ShugoYabuno/project-hanoji/marketing/sns/posts/index.md

# SNS投稿状況インデックス

最終更新: 2026-03-29

---

## 投稿済み（確認・記入用）

| 日付 | プラットフォーム | テーマ | URL / メモ | エンゲージメント |
|---|---|---|---|---|
| - | X | | | |
| - | note | | | |

※ Claude Desktopでアナリティクスを確認後、ここに記入してください。

---

## ブログ記事（note）の公開状況

| タイトル | 状態 | 公開URL |
|---|---|---|
| 自作レバーレス製作記 Vol.1：理想の角度を求めて失敗した話（v1） | 下書き済み | 未公開 |
| 自作レバーレス製作記 Vol.2：一体成形で「全部入り」を試みたら、印刷が地獄だった話（v2） | 下書き済み | 未公開 |
| v3〜v5 記事 | 未着手 | - |

---

## 下書き済みツイート

| ファイル | テーマ | 状態 |
|---|---|---|
| [2026-03-29_v5進捗.md](2026-03-29_v5進捗.md) | v5試作の進捗報告 | 下書き |
| [2026-03-29_コンセプト紹介.md](2026-03-29_コンセプト紹介.md) | なぜ作っているかの原点 | 下書き |
| [2026-03-29_v1失敗の話.md](2026-03-29_v1失敗の話.md) | v1の失敗→note誘導 | 下書き |
