ShugoYabuno/project-hanoji/content/blog/ideas/ideas.md

# ブログ記事・コンテンツアイデア帳

## 執筆方針
- **透明性 (Build in Public)**: 開発の過程、失敗、悩みもすべて公開し、ストーリーに共感してもらう。
- **専門性**: エルゴノミクスの知識や、なぜその形状に至ったかのロジックを語る。

---

## 記事ネタリスト

### 1. 宣言・コンセプト (The "Why")
**タイトル案**: 平面レバーレスで手首を痛めた私が、理想の「八の字」コントローラーを作るまで
- **構成**:
    - 既存レバーレスへの不満（手首の痛み、窮屈さ）
    - 「回内」と「回外」の解剖学的説明（図解を入れると良い）
    - Project Hanoji の構想（ラフスケッチ公開）
    - 目標：長くゲームを楽しむためのデバイスを作る

### 2. 開発ログ (The "How")
**タイトル案**: Project Hanoji 開発日誌 #1：3Dプリンターとの格闘
- **構成**:
    - 現在のFusion 360モデルの紹介
    - 印刷失敗写真（スパゲッティ状態など）をあえて載せる
    - 試作1号機の握り心地レビュー
    - 次の課題

### 3. こだわりポイント解説
**タイトル案**: なぜその角度？ボタン配置の数ミリ単位のこだわり
- **構成**:
    - 指の長さの違いに合わせたボタン配置
    - 天板の傾斜角（テント角）の検証プロセス
    - 15度？ 20度？ どの角度が最も楽か実験してみた

### 4. 部品選びの旅
**タイトル案**: 最高の打鍵感を求めて。キースイッチ選定会議
- **構成**:
    - 銀軸、ロープロファイルなど、採用候補のスイッチ比較
    - 静音性 vs クリック感
    - 実際に採用するスイッチの決定理由

### 5. マーケティング・戦略（裏側公開）
**タイトル案**: 個人開発デバイスをどうやって届けるか？Hanojiの販売戦略
- **構成**:
    - 個人メーカーとしての悩み
    - 価格設定の裏話
    - パッケージングへのこだわり

---

## SNS (X/Instagram) 投稿ネタ
- **[画像]**: 3D CADのワイヤーフレーム画像「設計中...」
- **[動画]**: 3Dプリンターが動いているタイムラプス
- **[画像]**: 試作機の基板配線の様子「配線地獄なう」
- **[質問]**: 「カラーバリエーション、どっちが好きですか？（A: マットブラック / B: ホワイト）」アンケート機能活用
