ShugoYabuno/project-hanoji/content/assets/prototypes/1/feedback.md

# プロトタイプ1 (v1) フィードバック

作成日: 2026-01-15
対象: 試作機v1 (@content/assets/prototypes/1)

## 検証結果・感想

### 1. 保持と安定性の問題
- **現象**: 傾斜（テンティング）がついているが、パームレストがついていない。
- **問題点**: 手が滑りやすく、常に手を特定の位置に保持するために力が必要となる。
- **対策案**:
    - 傾斜に追従するパームレストの実装が必須。
    - 表面の滑り止め加工や素材の検討が必要。

### 2. 角度設定の問題（手首への負荷）
- **現象**: テンティング角（z軸回転）はついているが、xy平面の角度（ハの字の開き角）がついていない。
- **問題点**:
    - 腕の自然な進入角度に対してキー配置が適合していない。
    - 結果として、手首を甲側（背屈方向）に無理に曲げる動作が強要される。
    - 手首への負荷が大きく、エルゴノミクスの目的（負荷軽減）が達成できていない。
- **対策案**:
    - テンティングだけでなく、左右のユニットをハの字に開く（またはその角度をつける）設計が必要。
