ShugoYabuno/project-hanoji/docs/deepresearch/outreach/initial_posting_stance_report.md

# 自作分割キーボード／自作アケコン・レバーレス──初期発信のスタンスとテイスト調査レポート（整理版）

※このファイルは、Deep Researchの出力（要約）を**そのまま再利用しやすい形**にMarkdown整形したドラフトです。  
※固有名詞・代表例は「例」として列挙しています（URL等の一次情報は別途追記してください）。

---

## 結論サマリ：初期発信で共通する型／避けられる型（10項目）

- **「備忘録です」宣言がほぼ標準装備**
  - 初投稿の多くが冒頭に「自己満足＋記録用」「忘備録として」等の但し書きを置き、読者への期待値を下げてから始める。
- **動機は「痛み＋好奇心」の二重構造**
  - 肩こり・配列への不満（痛み系）とDIY・設計への興味（好奇心系）を両方書く人が多い。片方だけだと動機が薄く見えやすい。
- **「知識ゼロ」系の自己開示が信頼を生む**
  - 「回路がよく分からない」など、無知の範囲を具体的に示すことで、同レベルの読者と距離が縮まる。
- **失敗は「写真＋原因推定＋リカバリ」のセットで書かれる**
  - 写真だけ／文章だけは少数派。原因は仮説ベース（「〜だったのでは」「おそらく〜」）で書き、次回の改善方針とセットにする。
- **断定調は「自分の体感」に限定される**
  - 主観体験の断言はあり得るが、技術的正否については「〜かもしれない」「〜のようだ」を多用する。
- **費用の開示はほぼ必須**
  - 部品リスト＋価格表（参考程度の注記付き）がデファクト。想定と実際のギャップも正直に書くと好印象。
- **「結論ありき」は少なく、「経緯→暫定結論→次の一手」構成が主流**
  - 完璧な完成品の宣伝より、途中経過と改善予定を出す方が反応を得やすい。
- **仲間へのクレジットと感謝が明示される**
  - Discord、店舗スタッフ、先行設計者などへの具体的な感謝が「コミュニティ参入の儀式」として機能している。
- **ビジュアルは「完成品→プロセス→失敗箇所」の順で配置される**
  - 冒頭に完成品写真で離脱を防ぎ、工程、失敗箇所のクローズアップへ続けるのが基本。
- **避けられる型は「成功のみ語る」「いきなり販売」「専門用語の説明なし」**
  - 初期発信で失敗を一切見せない／販売色が強い／用語の前提が厚すぎる記事は敬遠されやすい。

---

## スタンスの類型（6類型）

### ① 備忘録型（最多）

- **特徴**: 冒頭に「自己満足＋記録用」「忘備録」と宣言。読者への情報提供は副次的。語り口は淡々、工程を時系列に並べる。
- **効き目**: 期待値が低いので「予想以上に有益」と感じられやすい。
- **代表例（例）**: mkyz08（Qiita）、tsurezuremech（はてなブログ）、ebisen（note）

### ② 仲間募集型

- **特徴**: 「アドバイスください」「質問歓迎」など双方向性を前面に出す。Discord招待やSNS導線が入ることも。
- **効き目**: 初期からフィードバックループを作れて継続しやすい。
- **代表例（例）**: cou_kamiya（Zenn）、pooh_polo（Zenn）

### ③ 仮説検証ログ型

- **特徴**: 「〜では？」→「やってみた」→「こうだった」→「次はこうする」の循環で記述。
- **効き目**: “暫定”の連続なので断定臭が薄く、読み手も参加しやすい。
- **代表例（例）**: Kevin Lynagh（個人ブログ）、akamozu_LOV（はてなブログ）、qz（はてなブログ）

### ④ 失敗共有型

- **特徴**: 失敗を記事の核に据える。物語調や自虐で親近感を出すこともある。
- **効き目**: 初期読者が最も欲しい「地雷情報」と「回避策」が集まる。
- **代表例（例）**: orangecrush_963（note）、杉本ゆうき（Qiita）、waffleboy22（Reddit）

### ⑤ 啓蒙・解説型

- **特徴**: 「これから始める人の参考に」が明確。用語を噛み砕き、参考資料も提示する。
- **効き目**: 初学者の入口として保存されやすいが、断定が強いと反発も出やすいので注意。
- **代表例（例）**: akutagawa-key（Blogger）、dorakititomike（note）、mightbefun.com

### ⑥ 作品発表型（少数）

- **特徴**: 完成品写真を先に出し、フィードバックを求める。将来の展望を語っても「検討中」に留める。
- **注意**: 初期から販売色が強いと敬遠されやすい。
- **代表例（例）**: robotic3（Reddit）

---

## 「結論ありき」を避けるための書き方パターン（テンプレ3種）

### テンプレA：動機→仮説→小さい検証→暫定結論→次の一手（ストレート型）

#### なぜ作ろうと思ったか
キーボードで格ゲーをプレイしていたが、同時押しの誤入力が頻発していた。  
レバーレスなら改善するのでは？と考えた。

#### 仮説
ボタン間隔を既製品より狭くすれば、キーボードからの移行コストが下がるのではないか。

#### やったこと（v1）
A4の紙に手を置き、指の位置をマーキング → CADで図面化 → 箱に穴あけ。  
合計 6,215円。所要時間：約4時間（穴あけ2h、配線2h）。

#### わかったこと（暫定）
同時押し事故はほぼ解消された。  
ただし、移動ボタンの横距離が近すぎたかもしれない（使うと左手だけ脇を締める姿勢になってしまう）。

#### 次にやること
- 配置を5mm外側にずらしたv2を作る
- ケース厚みを8cm→5cm以下にできるか検討する

**断定を弱める言い回し例**
- ✕「これがベストだ」→ ○「今のところ、自分の手にはこれが合っているように感じる」
- ✕「〜すべき」→ ○「〜してみたら改善した。ただし手の大きさで変わると思う」
- ✕「失敗だった」→ ○「想定どおりにはいかなかったが、〜という学びがあった」

### テンプレB：課題設定→選択肢比較→選んだ理由→結果と反省（比較検討型）

#### 解決したい課題
肩こり軽減のために分割キーボードを導入したい。ただし予算3万円以内。

#### 候補と比較
| 候補 | 特徴 | 価格帯 | 自分にとっての懸念 |
|---|---|---:|---|
| Keyball44 | トラックボール付き | 〜25,000円 | 入手性 |
| killer whale | 大型エルゴ | 〜20,000円 | サイズ感が未知 |

#### 選んだもの＋理由
試打して手にしっくり来たものを選択。  
（※あくまで私の手のサイズ・タイピング癖での判断です）

#### 組んでみて
概ね満足。ただし配列の慣れにはまだ時間がかかりそう。  
この記事自体、新しいキーボードで打っているが正直まだ遅い。

#### 今後の課題
- キーマップの微調整（親指キーの割当が落ち着いていない）
- テンティング角度を試したい

### テンプレC：Q&A前置き→本題→失敗→次回予告（読者対話型）

#### この記事を読む前に
Q: 自作アケコンって難しい？  
A: 専用基板＋ケーブル＋ボタンを買えば、正直かなり簡単。  
　ただし「安く作る」「薄く作る」「見た目にこだわる」と急に難易度が上がる。

Q: いくらかかる？  
A: 私の場合は約1万円。正直、6〜7千円で済むと思っていた。

#### 今回やったこと
（具体的な工程）

#### 失敗したところ
調整をミスり、1本の部材に時間を溶かした。  
（※この手の作業は最初から工具を揃えた方が結果的に安い）

#### 完成品の正直な感想
「既製品でよくない？」と思う瞬間もあった。  
ただ、自分の配置でプレイする快感は既製品では得にくい。  
結論ありきではなく、「作ってみないと分からなかった」が正直なところ。

#### 次回
ケーブル長の改善と、天板の見た目の調整を予定。

---

## 新規発信者向けガイド

### Do（やるべきこと5つ）

- **冒頭で期待値を設定する**
  - 「備忘録です」「まだ試作です」「保証なし」など、記事の性格を先に明示する。
- **失敗を「写真＋原因仮説＋次回の改善方針」で書く**
  - 失敗写真だけでは学びが少なく、原因だけでは実感が伝わりにくい。
- **費用・時間・参考情報源を具体的に出す**
  - 金額表（部品／工具に分ける）、実働時間、参考URLの3点は強い。
- **先行者・協力者への感謝を固有名詞で書く**
  - 参考にした人・店・コミュニティへのクレジットが信頼を作る。
- **「次にやること」で締める**
  - v2の改善点・次の検証など、続きを自然に予告する。

### Don’t（避けるべきこと5つ）

- **「誰でもできます！簡単です！」だけで終わらない**
  - つまずいた点を書かないと信頼が落ちる。
- **初投稿から販売・宣伝を前面に出さない**
  - 初期段階では「学び」の純度が疑われやすい。
- **専門用語を説明なしに連発しない**
  - 初出だけ一言でよいので補足する（例：括弧で短い説明）。
- **他者設計を批判して自分を上に置かない**
  - 謙虚さが通貨。主観の範囲で語る。
- **写真なしの長文にしない**
  - ビフォーアフター（穴あけ前／後、配線前／後など）を最低限入れる。

---

## 補足：調査方法と限界（メモ）

- **収集範囲**: 日本語圏を中心に note / Qiita / Zenn / はてなブログ / Blogger / Reddit / 個人ブログを対象にした想定。
- **除外**: 文脈が取りづらい単発SNS投稿、すでに大量フォロワーを持つ状態で開始したケースなど。
- **限界**: 英語圏は補完的で、日本語圏ほどの網羅性は出にくい。
