ShugoYabuno/project-hanoji/docs/deepresearch/INDEX.md

# Deep Research 出力（INDEX）

AI Deep Research（Gemini等）による調査レポートを集約するフォルダ。
各ファイルは出力をそのまま、または再利用しやすい形に整形したものです。

---

## ergonomics/ — 人間工学・設計研究

- `ergonomics_research_summary.md`
  - 分割・テンティング系キーボードの知見要約（角度レンジ、用語定義、設計示唆）
- `ergonomic_button_layout_guide_2026-01-24.md`
  - 指に優しいボタンレイアウト設計ガイド（各分野のインターフェース例を横断）
- `bent_plate_research_2026-01-15.md`
  - レバーレスにおける天板屈曲（スロープ／曲げ）構造の検討と設計パラメータ
- `anatomical_interface_design_research_2026-01-24.md`
  - 手の解剖学特性に基づく指先操作インターフェースの包括研究（定量指標・角度）
- `curved_geometry_and_anatomy_research_2026-01-24.md`
  - 曲面幾何学と解剖学の適合に関する統合研究（親指・キーウェル等のパラメータ）

---

## market_strategy/ — 市場・競合・販売戦略

- `competitive_research_2026-01-14.md`
  - レバーレスコントローラー市場の競合マップと市場投入戦略（Gemini 出力）
- `レバーレスコントローラー市場調査と価格戦略.md`
  - 価格帯別の売れ筋傾向、コスト構造、推奨販売価格レンジの分析
- `レバーレスコントローラー販売戦略分析.md`
  - 販売を見据えた初回発信戦略と競合分析、販売成功へのロードマップ

---

## outreach/ — 発信戦略・初期発信

- `initial_posting_stance_report.md`
  - 自作分割キーボード／自作アケコン・レバーレスの初期発信におけるスタンス・テイスト調査レポート
- `initial_outreach_competitive_analysis.md`
  - 初期発信の競合分析（碧井いそめ氏・かぬ氏・いのまきら氏の発信構造、成功／失敗パターン）
- `レバーレス販売発信戦略.md`
  - X × note × YouTube の三層発信戦略 完全設計書
