ShugoYabuno/project-hanoji/docs/deepresearch/outreach/レバーレス販売発信戦略.md

# 自作レバーレスコントローラー販売のための発信戦略 完全設計書

---

## 結論：最適な投稿方針（1案）

**X（ほぼ毎日）× note（週1本）× YouTube（月2本）** の三層構造で、初期3か月は「販売」の文字を出さず、**「作る人」としてのキャラクター確立** に全リソースを投下する。

**運用比率：X 50% ／ note 30% ／ YouTube 20%**

- **X** ＝ フロー型。制作の「今」を高頻度で見せる場。写真1枚＋短文で日常的な接触頻度を確保する[^17]
- **note** ＝ ストック型。設計思想・試作記録・技術解説を体系的に蓄積し、検索経由での新規流入を狙う[^24]
- **YouTube** ＝ 体験証明型。組み立て配信・打鍵音・実際のプレイ映像で「この製品は本物だ」と伝える[^42]

---

## 1. 調査から判明した成功パターン3つ

### ① 制作過程の「全公開」戦略

碧井工房（JumpHack）は、Xで制作過程を日々ポストし、BOOTHと自社ストアで組み立てキット＋完成品の2形態で販売している[^33][^39]。YouTubeでは組み立てライブ配信を行い、視聴者がリアルタイムで質問できる形式を採用した[^42]。「プロトタイプ段階から公開する」「図面データすら公開する」という透明性が、ニッチコミュニティでの信頼獲得に直結している。

### ② 媒体横断のクロスポスト設計

投稿データ分析では、noteとXを連携させることで単独利用時よりリーチが伸びる傾向が示唆されている[^17]。具体的には、noteの冒頭部分だけXで紹介し「続きはnoteで」と誘導するパターン、Xで集まった質問をnoteでまとめ記事化するパターンが特に有効である。

### ③ 「ユーザー参加型」のコミュニティ形成

P-3 Controller（ぴくるす）はXでプレゼント企画を実施し、レバーレス完成品を提供することでフォロワーとの接点を生んでいる[^23][^26]。また遊舎工房（自作キーボード）は「コミュニティと一緒に成長する」を運営方針に掲げ、グループバイで300台（国内50台・海外250台）を販売した実績がある[^20]。

---

## 2. 避けるべきパターン3つ

### ❌ 初期から「販売臭」を出す
noteに投稿する記事が最初から商品の宣伝ばかりでは、読者はなかなか増えない。まず消費者目線で役に立つ情報を発信し、フォロワーを増やしながらブランドへの共感を育てることが先決[^27]。

### ❌ 過剰投稿によるファン離れ
投稿頻度が高すぎるとアンフォロー率が上がる傾向がある。質と量のバランスが崩れると逆効果になりやすい[^17]。

### ❌ 同一コンテンツのコピー投稿
noteの記事をそのままXのスレッドに貼り付ける、リンクだけを機械的に共有する自動投稿は効果が限定的。各プラットフォームで異なる価値を提供する必要がある[^17]。

---

## 3. テーマ配分の最適比率

| テーマカテゴリ | 全体比率 | 主な媒体 | 具体例 |
|---|---|---|---|
| 試作記録・制作過程 | 30% | X, YouTube | 部材到着、組み立て中の写真、ライブ配信 |
| 技術解説・設計思想 | 25% | note | GP2040-CE解説、ボタンレイアウト理論、素材選定理由 |
| 失敗談・改善プロセス | 15% | note, X | 基盤ネジ穴の失敗[^16]、設計ミスからの修正 |
| 使用感・プレイ体験 | 15% | YouTube, X | 打鍵音ASMR、実プレイ映像、操作比較 |
| コミュニティ交流 | 10% | X | 他制作者の紹介、質問回答、アンケート |
| 販売準備・告知 | 5% | X, note | 価格検討中の匂わせ、予約開始告知 |

**重要：初期3か月は「販売準備・告知」の比率を5%以下に抑え、試作記録＋技術解説で全体の55%を占めるようにする。**

---

## 4. 媒体別の役割と最適投稿サイクル

### X（フロー＝日常接触）

- **頻度**：ほぼ毎日（最低でも数日に1回は継続する）[^17]
- **最適時間帯**：平日昼・夕方に反応が伸びやすい傾向[^17]
- **コンテンツ形式**：写真1枚＋短文、スレッド形式の制作メモ、アンケート
- **週1-2回**はスレッド形式での深掘りコンテンツを投稿

### note（ストック＝資産蓄積）

- **頻度**：週1本（個人アカウントは週1-2回の継続が現実的）[^17][^22]
- **最適時間帯**：日曜夜・平日夜に反応が伸びやすい傾向[^17]
- **コンテンツ形式**：2,000-5,000字程度の長文が目安。月1回は深掘り記事を入れる[^17]
- **SEO意識**：「レバーレス 自作」「アケコン 作り方」等のキーワードをタイトル・見出しに配置[^24]

### YouTube（体験証明＝信頼構築）

- **頻度**：月2本（負担とクオリティのバランス）
- **コンテンツ形式**：制作工程動画（長尺OK。作りたい人向けは長めの方が評価されやすい傾向）[^31]、組み立てライブ配信、打鍵音・使用感レビュー
- **概要欄にnoteとXへのリンクを必ず設置**[^24]

---

## 5. 最初の3か月の投稿設計テンプレート

### 第1フェーズ（1か月目）：「何を作ろうとしているか」を見せる

**目標**：格ゲーコミュニティ内での認知獲得、フォロワー50人

| 週 | X（毎日） | note（週1） | YouTube |
|---|---|---|---|
| 1週目 | 使用素材の写真、RP2040-Picoの紹介 | 「なぜ自作レバーレスを作るのか」（設計思想・動機） | — |
| 2週目 | ボタンレイアウトの検討過程、CAD画面 | 「レバーレスの仕組みをゼロから解説」（技術入門） | 部材開封・紹介動画（5-8分） |
| 3週目 | 発注したアクリル板の到着報告、寸法確認 | 「試作1号機の設計で考えたこと」（素材・構造選定） | — |
| 4週目 | 組み立て開始の写真、困った点メモ | 「試作1号機の組み立てで起きたトラブル」（失敗談） | 組み立て過程のタイムラプス動画 |

### 第2フェーズ（2か月目）：「試行錯誤の過程」を共有する

**目標**：フォロワー150人、note記事のスキ数平均20以上

| 週 | X（毎日） | note（週1） | YouTube |
|---|---|---|---|
| 5週目 | 試作1号機の完成写真、打鍵テスト | 「1号機完成レビュー：良い点と改善点」 | 打鍵音ASMR＋実プレイ映像 |
| 6週目 | 改善ポイントの洗い出し、他製品との比較 | 「GP2040-CEのファームウェア設定ガイド」（技術解説） | — |
| 7週目 | 2号機の設計変更点、スケッチ公開 | 「ボタン配置の人間工学を考える」（設計思想） | — |
| 8週目 | 2号機組み立て中、「これ売ってほしい？」アンケート | 「1号機→2号機で何を変えたか」（改善記録） | 2号機の組み立てライブ配信 |

### 第3フェーズ（3か月目）：「完成度の高さ」を証明し、販売を匂わせる

**目標**：フォロワー300人、DM/リプで「販売しないの？」の声が出る

| 週 | X（毎日） | note（週1） | YouTube |
|---|---|---|---|
| 9週目 | 2号機完成写真（高品質な撮影）、仕様スペック | 「2号機完全レビュー：市販品との比較」 | 完成品レビュー＋プレイ映像（勝率変化等） |
| 10週目 | オフ対戦会での使用報告、他プレイヤーの反応 | 「自作レバーレスにかかったコスト全公開」（費用明細） | — |
| 11週目 | 「量産に向けて検討中」と自然に言及 | 「3か月の制作で学んだこと総まとめ」 | 1号機→2号機の進化を振り返る比較動画 |
| 12週目 | 販売形態の検討（キット or 完成品）アンケート | 「販売に向けて：価格設定の考え方」 | — |

---

## 6. 初期フェーズで「販売臭」を出す最適濃度

**結論：最初の8週間は販売意図ゼロ。9週目以降に10-15%程度まで徐々に引き上げる。**

| フェーズ | 期間 | 販売臭の濃度 | 具体的な匂わせ方 |
|---|---|---|---|
| 純粋な制作者 | 1-4週 | 0% | 一切販売に言及しない。「自分が使いたくて作っている」スタンス |
| 共感者の登場 | 5-8週 | 5% | 「欲しいって言ってくれる人がいて嬉しい」とリプ引用RT程度 |
| 需要の可視化 | 9-10週 | 10% | Xアンケート「もし売るとしたらいくらなら買う？」 |
| 販売の自然な流れ | 11-12週 | 15% | 「量産コスト計算中」「販売方法を調べている」と過程を公開 |
| 販売開始 | 13週以降 | 20% | BOOTH/BASEリンク公開。ただし投稿全体の8割は制作・技術コンテンツ維持 |

碧井工房（JumpHack）のケースでは、プロトタイプ段階から「実験的な開発機なので、販売の意図にご理解いただける方のみ購入してください」と透明な姿勢で販売を開始し、テック系メディアにもレビュー記事が掲載される結果につながった[^39][^46]。

---

## 7. 投稿方針のKPI候補

### 初期（1-4週）：認知フェーズ

| KPI | 目標値 | 測定方法 |
|---|---|---|
| Xフォロワー数 | 50 | プロフィール |
| Xインプレッション/投稿 | 500 | X Analytics |
| note PV/記事 | 100 | noteダッシュボード |
| noteスキ数/記事 | 10 | noteダッシュボード |

### 中期（5-8週）：エンゲージメントフェーズ

| KPI | 目標値 | 測定方法 |
|---|---|---|
| Xフォロワー数 | 150 | プロフィール |
| Xエンゲージメント率 | 3%以上 | (いいね+RT+リプ)÷インプ |
| note保存率 | 5%以上 | スキ数÷PV |
| YouTube視聴維持率 | 40%以上 | YouTube Studio |
| DM・リプでの質問件数 | 週3件以上 | 手動カウント |

### 後期（9-12週）：需要検証フェーズ

| KPI | 目標値 | 測定方法 |
|---|---|---|
| Xフォロワー数 | 300 | プロフィール |
| 「販売してほしい」系リプ・DM | 累計10件以上 | 手動カウント |
| アンケート回答数 | 30以上 | X投票機能 |
| noteからBOOTH/BASEへの遷移 | 月50クリック | リンク計測ツール |
| YouTube登録者数 | 50 | YouTube Studio |

**最重要KPI：「販売してほしい」の声の件数。** これが自然発生しない場合、コンテンツの方向性か製品の魅力に課題がある[^52]。

---

## 8. 反応が良い投稿の特徴

実在する自作アケコン制作者のnote記事・X投稿を分析した結果、以下の特徴が反応を集めていた。

### 高反応の投稿パターン

- **失敗談＋リカバリー**：「基盤のネジ穴設計を完全に失敗しました」→写真→「こう直しました」の流れ[^16]
- **ビフォーアフター写真**：試作1号機と改良版の並び写真
- **費用の透明公開**：「ざっくり6万円かかりました」「20,000円以下を目標に挑戦」[^6][^16]
- **図面・データの無料公開**：CADデータやレイアウト寸法の共有が信頼感を醸成[^16]
- **実プレイでの成果報告**：「このレバーレスで27連勝し、無敗でダイヤ5突破」のような具体的数字[^46]

### 低反応の投稿パターン

- スペック羅列のみで過程がない投稿
- 写真なしのテキストのみ報告
- 購入リンクだけの宣伝投稿

---

## 9. 初回〜第5回までの記事テーマ案（note）

| 回 | タイトル案 | 文字数目安 | カテゴリ |
|---|---|---|---|
| 第1回 | 「格ゲー歴○年の自分が"理想のレバーレス"を自作することにした理由」 | 3,000字 | 設計思想・動機 |
| 第2回 | 「レバーレスコントローラーの仕組みを完全図解【初心者向け】」 | 4,000字 | 技術解説 |
| 第3回 | 「試作1号機の全記録：設計→発注→組み立てで起きたこと」 | 5,000字 | 試作記録・失敗談 |
| 第4回 | 「ボタン配置の"正解"を探す旅：人間工学×格ゲー操作論」 | 3,500字 | 設計思想 |
| 第5回 | 「1号機を1か月使ってみた正直レビュー＆2号機で変えること」 | 3,000字 | 使用感・改善 |

第1回は設計思想・動機から始め、人となりと目的を明確にする。第2回で技術的な信頼性を担保し、第3回で「一緒に作っている」感覚を持たせる。第4回で専門性を示し、第5回で正直さと改善意欲を見せる。この流れで「この人から買いたい」という信頼が醸成される[^24][^27]。

---

## 10. クロスポスト運用の実践フロー

note記事公開日（例：毎週日曜20:00）を基準に、以下の5ステップで設計する[^17]。

1. **公開1-2日前（金-土）**：Xで「次のnote記事は○○について書いてます」と予告
2. **公開当日（日曜20:00）**：noteに本投稿。直後にXで要点3つをスレッド形式で紹介＋noteリンク
3. **翌日昼（月曜12:00）**：Xで「昨日の記事、こんな反応いただきました」と再シェア[^19]
4. **公開3日後（水曜）**：読者の質問やコメントに回答するXスレッド
5. **公開1週間後**：次回記事の予告に前回記事リンクを添える

この再通知設計により、週1本のnote記事でも実質週5回の露出が生まれる[^19]。

---

## 参考：実在する個人工房の発信パターン

| 工房名 | 主力製品 | 主な販売先 | X活用 | note/ブログ活用 | YouTube活用 |
|---|---|---|---|---|---|
| 碧井工房（JumpHack） | スト6向けレバーレス | BOOTH, 自社ストア | 日々の制作ポスト[^33] | — | 組み立てライブ配信[^42] |
| P-3 Controller | アクリル製レバーレス | BASE, BOOTH | 製品紹介＋プレゼント企画[^23] | — | 製品紹介動画[^21] |
| それいる工房（Siro） | カスタムボタン・塗装 | BASE | 日常＋作品画像[^25] | — | 自作アケコン製作記シリーズ[^25] |
| 遊舎工房（自作KB参考） | 自作キーボードキット | 実店舗＋EC | SNSで頒布活動[^18] | — | — |

全工房に共通するのは、**販売開始前から制作過程を公開し、コミュニティとの対話を通じて需要を確認してから販売に踏み切っている** 点である[^49]。

---

## まとめ：実行チェックリスト

- [ ] X/note/YouTubeのアカウント開設。プロフィールに「自作レバーレス制作中」と明記
- [ ] 第1回note記事（動機・設計思想）を公開
- [ ] Xで毎日1投稿を2週間継続
- [ ] 月2本のYouTube動画（開封＋組み立て）をアップ
- [ ] 8週目にXアンケートで需要調査
- [ ] 12週目までにBOOTH/BASEの販売ページ準備
- [ ] 「販売してほしい」の声が10件以上集まったら販売開始を告知

---

## References

6. [レバーレスコントローラーを自作した話。｜たくみ](https://note.com/kumichang0406/n/n669866938393) - 今はアケコン用の基盤が売っているので自作のハードルは下がってる感じですね。 基盤(配線)・ボタン・ケースがあれば作れるぞ！！！ 半年ぐらい前に完成して ...

16. [【これを見れば作れます】超薄型レバーレスアケコンの制作方法 ...](https://note.com/kinghalo_dl/n/nba75df864ed0) - 自作の超薄型レバーレス完成した！予想の100倍市販品っぽい完成度になって嬉しい。 サイズは縦横260mm×200mmでB5用紙くらいの大きさで ...

17. [データで見る！noteとXの最適投稿サイクルとクロスポスト戦略](https://note.com/takeuchi_posts/n/n8d1b1a190f4e) - 最低でも3日に1回は投稿が必要（アルゴリズム対策）. 企業アカウントの最適頻度: 平日は1日2-4回の投稿が最適. 同じ内容でも ...

18. [初心者でも3時間で自作キーボードが作れる！？遊舎工房さんに ...](https://goworkship.com/magazine/keyboard-handmade/) - 遊舎工房代表。2017年頃に自作キーボードに目覚め、SNSやイベントでHelixキーボードキットを頒布。その売り上げを元手に専門通販サイトを立ち上げ ...

19. [note投稿頻度の最適解｜AI×テンプレで続く“週3戦略”｜そうた](https://note.com/kotobashira/n/n57cffc8f4dad) - これだけで、1本の記事が“3回露出”する。つまり週3投稿＝実質週9アクションになる。毎日投稿しても読まれない記事を量産するより、「読まれる仕掛け ...

20. [自作キーボードの聖地「遊舎工房」買収の経緯を訊くーー急成長 ...](https://fabscene.com/new/special/yushakobo-ma-ceo-interview-growth-challenges/) - 自作キーボードの聖地・遊舎工房が嘉穂無線HDに買収された背景を、創業者の倉内誠氏と新オーナーの柳瀬隆志社長が語る。急成長の裏にあった経営課題 ...

21. [【11ボタンレバーレス】安くておすすめな自作キット出ました【スト6】](https://www.youtube.com/watch?v=R_qhazi21tI) - 今回も僕の工房のコントローラーを紹介しました。 皆でアクリル板を愛でよう！！！ ↓BASEショップ↓(キット＆完成品メイン) https://ppp3con.base.shop/ ...

22. [【note運用の深層分析】読まれる人がやっている「投稿頻度と ...](https://note.com/ricca_2525/n/n90c81f1e78cd) - 読者の立場で考えると、「更新が楽しみ」と思える頻度は＂忘れられないくらいの間隔＂です。 具体的には週1〜2回。 少なすぎると存在を忘れられ、多すぎると ...

23. [P-3 Controller@アケコン工房 (@p3_con) / Highlights / X](https://x.com/p3_con/highlights) - アクリル製レバーレスコントローラーの製作・販売をしています ⭐︎ケース/組立キット/完成品など⭐︎ BASE(販売) ppp3con.base.shop. BOOTH(販売) ppp-con.boot...

24. [noteを使った集客方法とファン作りに上手く活用する手段](https://note.com/mexce/n/n9cfb36c47cd6) - noteを使った集客の主な流れについて · アプローチしたいターゲットを決める · コンテンツ戦略を立案する · 販売している商品（サービス）へ誘導する.

25. [【自作アケコン製作記】知識ゼロから始める自作アケコン【基板編】](https://www.youtube.com/watch?v=QY2ZvpV4nJM) - ... YouTubeの動画はコメントありきのいい動画だと思っています！ コメント ... コントローラーのカスタムボタンや皆さんの「それいる」なものを提供する工房その ...

26. [P-3 Controller@アケコン工房 (@p3_con) / Posts / X](https://x.com/p3_con) - 【固定用リンク集】 アクリル製レバーレスコントローラーの製作・販売をしています ⭐︎ケース/組立キット/完成品など⭐︎ BASE(販売) ppp3con.base.shop

27. [noteをECの集客やファン作りに活用するには？コンテンツ ...](https://www.hit-mall.jp/blog/management/column-043.html) - noteをECの集客やファン作りに活用するには？コンテンツマーケティングのコツをnoteさんに聞いてみた. SEO対策 · コンテンツ制作 · プロモーション.

31. [動画は素人でも予算をかけず自前で作れる！ 『仕事に使える動画術 ...](https://markezine.jp/article/detail/22730) - 仕事に使える動画術 成功例に学ぶYouTube活用とオリジナル動画作成法 著者：家子史穂、千崎達也 出版社：翔泳社 発売日：2015年7月13日 価格：1,800円（ ...

33. [碧井いそめ](https://x.com/isomeaoi/status/1736785157896704214) - ... 工房（BOOTH ... ここ数ヶ月レバーレス制作にどっぷりはまっていて、自作のコントローラを販売しています。自作レバーレスの名前は「JumpHack」です！

39. [スト6向けレバーレスJumpHack03プロトタイプ（組み立てキット）](https://booth.pm/ja/items/5317422) - 在庫なし

42. [【碧井工房】スト6向け新レバーレス JumpHack 01を自作してみる ...](https://www.youtube.com/watch?v=-vgepu3GC5Q) - ... レバーレス JumpHack 01を自作してみるよー. 5K views · Streamed 1 year ago. #レバーレス #ストリートファイター6 #スト6 ...more. 碧井...

46. [アケコン自作キットに挑戦。レバーレスコントローラー ...](https://www.techno-edge.net/article/2024/03/25/3038.html) - ストリートファイター6向けのレバーレスコントローラーを開発・販売している碧井工房の「JumpHack03」のキットを組み立ててみました。

49. [eSports界注目の「自作アーケードコントローラー」とは - FabScene](https://fabscene.com/new/special/leverless-controller-fighting-games/) - ストリートファイター6で人気のレバーレスコントローラーを自作する魅力を紹介。オープンソースプロジェクトGP2040-CEやFlatboxを活用し、3000円程度 ...

52. [BOKURAが考えるファン創りとは](https://bokura.biz/bokura%E3%81%8C%E8%80%83%E3%81%88%E3%82%8B%E3%80%81%E3%83%95%E3%82%A1%E3%83%B3%E5%89%B5%E3%82%8A%E3%81%A8%E3%81%AF/) - BtoCの企業の場合、全体売上の8割が顧客全体の2割で占められていると言われています。 ... ファン心理に基づいたコンテンツ制作. 前述で設定したKPIを達成 ...
