ShugoYabuno/project-hanoji/docs/deepresearch/market_strategy/レバーレスコントローラー市場調査と価格戦略.md

# **自作レバーレスコントローラー市場における参入戦略と価格最適化に関する調査報告書**

## **1\. 結論：個人クリエイターが採るべき市場ポジションと販売戦略**

自作レバーレスコントローラー市場は現在、歴史的な転換点にある。2023年の『ストリートファイター6』の発売以降、需要が爆発的に増加した一方で、中国系メーカーによる圧倒的な量産効果を背景とした「低価格・高性能モデル」の波が押し寄せ、個人クリエイターの立ち位置が極めて限定的になっているからである 1。本調査に基づく結論として、個人クリエイターが持続可能な利益を確保しつつ、熱狂的なファンを獲得するために推奨される戦略を以下に提示する。

### **最有力な販売価格レンジと戦略的判断**

個人クリエイターが目指すべき最も有力な販売価格帯は、22,000円から28,000円（税込・送料別）のレンジである。この価格帯は、1万円台で流通するHaute42等の「量産型格安モデル」に対する明確な品質・意匠の差別化を打ち出しつつ、4万円を超えるRazer KitsuneやVictrix Pro FS-12といった「大手ブランドのハイエンドモデル」を検討する層に対して、同等のスペックまたはそれ以上のカスタマイズ性を提示できる「スイートスポット」である 2。

このレンジでの販売を成功させるためには、単なる「Hitboxのクローン」ではなく、特定のプレイスタイルに特化した付加価値が必須となる。具体的には、GP2040-CEを基板に採用して低遅延を実現しつつ、アクリル積層や3Dプリント筐体による独自の「打鍵感」と「静音性」、そして昨今の格闘ゲームにおける「多ボタン化（14〜16ボタン）」への対応が、購入の決定打となる 3。

### **初期販売における推奨プラン**

初期販売においては、以下の「少数限定・即納モデル」による展開を強く推奨する。

| 項目 | 推奨内容 | 理由 |
| :---- | :---- | :---- |
| **初期販売価格** | **23,800円** | 材料費・加工費を回収しつつ、1万円程度の純利益を確保できる設定。 |
| **販売形式** | **少数ロット（5〜10台）即納販売** | 受注生産は納期管理のリスクが高く、ユーザーは「今すぐ遊びたい」という欲求が強いため。 3 |
| **主要チャネル** | **Booth** | 国内ターゲットへの到達率が高く、SNSでの拡散と親和性が極めて高いため。 3 |
| **差別化軸** | **SF6特化の独自配置と静音化** | 既存品にないボタン位置と、日本の住環境に適した「静音」は常に需要がある。 3 |

### **避けるべき価格帯とその根拠**

* **15,000円未満**: この価格帯は、Haute42やFightbox等の中国製量産機が支配している。個人クリエイターが単品でパーツを調達し、組み立てにかかる工数を考慮すると、利益率は極めて低く、価格競争で疲弊するリスクが極めて高い 1。  
* **30,000円〜38,000円の「中途半端なスペック」層**: この価格帯に設定する場合、PS5へのネイティブ対応（Brook基板等の搭載）が期待される。PC専用機でありながらこの価格に設定すると、ユーザーは「もう少し出してVictrixを買う」か「2万円台の個人制作モデルを買う」かの二択になり、需要が蒸発しやすい 2。

## ---

**2\. 価格帯別の売れ筋傾向と市場構造の分析**

現在のレバーレスコントローラー市場は、搭載される制御基板、筐体素材、およびターゲットとするハードウェアによって、4つの主要な価格帯に分断されている。

### **価格帯別の売れ筋傾向まとめ**

| 価格帯 | 主な素材・仕様 | 対応ハード | 主な販売チャネル | 売れ筋傾向と特徴 |
| :---- | :---- | :---- | :---- | :---- |
| **1万円台（格安）** | 薄型アクリル、小型PCB、量産スイッチ | PC, Switch | Etsy, Amazon, AliExpress | Haute42等の量産モデルが圧倒。安価にレバーレスを試したい層に売れる。 1 |
| **2万円台（普及・個人）** | アクリル積層、3Dプリント、ホットスワップ | PC, PS4 (パススルー) | Booth, Etsy | 個人クリエイターの主戦場。14〜16ボタンの多ボタンモデルが最も売れる。 3 |
| **3万円台（中堅・高品質）** | 金属、高級ウッド、Brook基板 | PS5対応 | Booth, 公式店 | 競技志向ユーザー。PS5での安定動作とビルドクオリティが求められる。 2 |
| **4万円以上（高級）** | アルミ筐体、ブランド品、公式ライセンス | 全ハード | 大手ストア, 公式直販 | Razer, Victrix等。プロ使用の信頼性と所有欲を満たすデザイン。 2 |

### **1万円台以下の市場：量産モデルの破壊的影響**

この価格帯は、2023年後半から登場した中国メーカーの製品により、市場ルールが完全に書き換えられた。特にHaute42シリーズは、G16やS16といったモデルを50ドルから80ドル程度で提供しており、RGB LED、OLEDディスプレイ、Kailhロープロファイルスイッチを標準装備している 1。 Etsyにおける「Hitbox-Style Flatbox」などの個人出品も、かつては100ドル前後で売れていたが、現在は価格を下げざるを得ないか、あるいは「Haute42のアートプリントサービス」といった周辺ビジネスへの転換を余儀なくされている 6。個人クリエイターがこの価格帯で勝負することは、材料費（基板、スイッチ、アクリル板、ネジ類）と加工費（レーザーカットや3Dプリント時間）を積み上げると、もはやボランティアに近い活動となる。

### **2万円台の市場：個人クリエイターの黄金圏**

Boothにおける「BridgeBoard（18,500円）」や「Fighting Dog Board（25,600円）」といった製品が、販売開始数分で完売する現象はこの価格帯で起きている 3。この層のユーザーは、「1万円台の格安機では満足できないが、4万円以上のブランド品は高すぎる」と感じており、かつ「自分の好きなイラストを入れたい」「特定のボタン配置でプレイしたい」という強いこだわりを持っている。 売れ筋の条件は、単なる12ボタンではなく、近年の格闘ゲームのシステム（『ストリートファイター6』のドライブインパクトやパリィ）に最適化された、親指や小指付近の「ボタン増設」である 3。また、筐体の厚みを15mm〜20mm程度に抑えた「薄型」であることも、持ち運びや膝置きプレイを重視する層から高く支持されている 2。

### **3万円以上の市場：信頼性とブランドの領域**

3万円を超えるモデルにおいて、ユーザーが最も重視するのは「PS5への完全対応」である。Brook社製の「UFB Fusion」などの基板を搭載したモデルは、基板単体で1.5万円から2万円近いコストがかかるため、製品価格は必然的に3万円台後半から4万円台となる 4。 Etsyでは、高級ウッド（マホガニーやウォルナット）を使用したモデルが300ドルから700ドルで取引されており、もはや入力デバイスではなく「工芸品」としての価値を確立している 6。また、Razer Kitsune（約4.9万円）のように、光学式スイッチによる超高速反応と、ソニーの公式ライセンスによる「大会での動作保証」を武器にする大手メーカーとの競合になるため、個人がここを攻めるには極めて高いブランド力か、ニッチなエルゴノミクス（人間工学）デザインが必要となる 2。

## ---

**3\. 技術仕様とコスト構造：価格を決定付ける要因**

レバーレスコントローラーの販売価格を構成する要素は、主に「基板（ファームウェア）」「スイッチ」「筐体素材」の3点に集約される。これらをどのように選択するかが、利益率とターゲット層の満足度に直結する。

### **制御基板（PCB）とファームウェアの選択**

制御基板は、製品の「心臓部」であり、対応ハードウェアと遅延性能を決定する。

* **GP2040-CE (Raspberry Pi Pico系)**: 現在の自作市場における圧倒的な主流である。基板自体のコストが1,000円以下と極めて安価でありながら、1ms以下の超低遅延を実現している 4。PC環境でのプレイが主体のユーザーにとっては最良の選択肢となる。一方で、PS5で使用するためには「USBパススルー」ポートを設け、別売のドングル（MagicBoots等）を接続させる必要がある 5。  
* **Brook社製基板**: 「UFB Fusion」や「P5 Plus」などの基板は、PS5へのネイティブ対応を謳っており、コンバーターなしで安定した動作を保証する。しかし、GP2040-CE搭載機に比べて販売価格を7,000円から15,000円ほど引き上げる要因となる 4。この価格差は、初心者には高く感じられるが、オフライン大会に参加する競技層には「必須の投資」として受け入れられる。

### **キースイッチとボタンキャップの進化**

ボタンの押し心地は、レバーレスの「評価」を決定する。

* **Cherry MX互換スイッチ**: カスタマイズ性が高く、銀軸（Speed Silver）などは格闘ゲーム向きとされる 4。GamerFingerのような高級ボタン（1個1,000円前後）を採用すると、12〜16ボタン構成ではボタン代だけで1万円を超えることになり、高価格帯モデルへの採用が主となる 1。  
* **Kailh Low Profile (Choc v1/v2)**: 薄型筐体を実現するための必須パーツである。Haute42やSnackbox Microに採用されており、現在主流の「薄型レバーレス」のスタンダードとなっている 6。特にChoc v2は、Cherry MX用のボタンキャップが流用できるため、個人クリエイターにとって意匠の幅を広げやすい選択肢である 6。

### **筐体素材による差別化と加工コスト**

筐体は、ユーザーが直接触れる部分であり、コストと「格付け」に大きく寄与する。

* **アクリル積層**: 数枚のアクリル板を重ねる手法で、自作レバーレスでは最も一般的である。天板にイラストを挟むことが容易で、個人クリエイターの「表現力」を発揮しやすい 3。一方で、アクリル自体の重量や、エッジの処理（面取り）の丁寧さが、2万円台と3万円台を分ける境界線となる。  
* **3Dプリント (PLA / Resin)**: 自由な造形が可能で、複雑なエルゴノミクス配置を実現できる。しかし、安価なPLA出力では「チープなプラスチック感」が出やすく、高級感を出すには高品質なレジン（樹脂）出力や、丹念な研磨・塗装が求められる 6。  
* **アルミニウム・金属**: CNC加工によるアルミ筐体は、最高の剛性と高級感を提供するが、小ロットでの制作コストは極めて高い。Haute42のMシリーズ（約1.5万円）のように、量産によってこの素材を低価格で提供するメーカーが現れたことで、個人がアルミ筐体で価格競争を行うことは困難になっている 1。

## ---

**4\. 売れる価格帯の条件と「高単価でも売れる」理由の深掘り**

単なるスペック比較では、個人クリエイターは大手や中国メーカーに勝つことはできない。しかし、現実には3万円前後の自作モデルが飛ぶように売れている。その背景には、特定の「購入動機」が存在する。

### **成功している自作モデルの共通条件**

売れている個人制作のレバーレスには、以下の3つの要素が必ず備わっている。

1. **「痒い所に手が届く」ボタン配置**: 標準的なレバーレス配置に加え、左手小指の位置に「パリィボタン」を置いたり、右手親指の位置を2つに増やしたりするなど、格闘ゲームの最新トレンドに即応した配置を提供している 3。これは、金型を作って大量生産する大手メーカーには不可能な、小回りの利く個人クリエイターならではの強みである。  
2. **徹底した「静音」への配慮**: 日本の住環境において、アケコンの打鍵音は常に問題となる。静音スイッチの採用だけでなく、筐体内部にフォームを詰めたり、Oリングを標準装備したりするなど、「届いてすぐに静かに使える」ことは、2万円以上の支出を厭わない層にとって大きな魅力である 4。  
3. **作者の「顔」が見える信頼感**: Boothでの販売において、作者がSNSで開発状況を公開し、ユーザーの質問に丁寧に答えている場合、それは「サポートの保証」として機能する。海外の量産品は故障時の対応に不安があるが、国内のクリエイターであれば修理や相談が可能であるという期待が、数千円の価格差を埋めている 3。

### **高価格（4万円以上）でも売れる理由**

この領域では、デバイスとしての機能よりも「プロ仕様」であることや「唯一無二の所有感」が優先される。

* **競技基準のクリア**: 公式ライセンス品であることは、Sonyのアップデートによって突然使えなくなるリスク（いわゆる「8分認証」問題）がないことを意味する。プロゲーマーや、その予備軍にとって、この「安心感」は4万円を支払う価値がある 4。  
* **素材の希少性と美学**: Etsyで見られる「Bishop|Select Maestro」などの木製モデルは、700ドル近い価格設定ながら、その工芸品としての美しさでニッチなファンを掴んでいる 6。機能が同等であれば、人は「より美しいもの」に投資する。

## ---

**5\. 想定販売価格帯の推奨レンジ：コスト・競合・提供価値の相関分析**

本調査の結果に基づき、新規参入する個人クリエイターが検討すべき2つの価格戦略案を提示する。

### **推奨案①：戦略的ミドルレンジ（本命）**

* **価格設定**: **22,000円 〜 25,800円**  
* **構成**: GP2040-CE / 14〜16ボタン / アクリル積層（天板着せ替え対応） / 静音化済  
* **理由**:  
  * **コスト面**: 部材費（約8,000円〜10,000円）＋加工外注費（約3,000円）に対し、約1万円の利益を確保できる。  
  * **競合面**: 1万円台の格安機ユーザーの「アップグレード需要」を拾える。  
  * **提供価値**: 「自分だけの配置」「自分だけのイラスト」という、最も熱量の高いニーズに応えることができる 3。

### **推奨案②：ハイエンド・プロトタイプ（高単価狙い）**

* **価格設定**: **38,000円 〜 45,000円**  
* **構成**: Brook P5 Plus（PS5ネイティブ対応） / アルミ・ウッド混合筐体 / ハイエンドスイッチ（GamerFinger等）  
* **理由**:  
  * **コスト面**: 部材費だけで2万円を超えるが、PS5対応という明確な付加価値がある。  
  * **競合面**: Razer Kitsune（約4.9万円）と比較され、「同等性能でよりコンパクト、かつボタン配置が優れている」という文脈で勝負する。  
  * **提供価値**: コンバーター不要の利便性と、最高級のパーツによる所有感を提供できる 2。

## ---

**6\. 販売チャネルと配送戦略の最適化**

販売する場所と方法は、最終的な手残り利益とブランドイメージに直結する。

### **販売プラットフォームの特性比較**

| プラットフォーム | メリット | デメリット | 適した戦略 |
| :---- | :---- | :---- | :---- |
| **Booth** | 手数料が安い(5.6%)、国内ファン層に直結、匿名配送可能。 | 海外への直接販売は転送サービス頼み。 | 日本国内の主力チャネル 3 |
| **Etsy** | 世界中のファンにリーチ、単価を上げやすい。 | 手数料体系が複雑、送料が高い、関税トラブル。 | 独自の意匠を持つ高級モデルの海外展開 6 |
| **Mercari** | 集客力が極めて高い、即決性が強い。 | ブランド化しにくい、値切り交渉が多い。 | 試作品や、知名度向上前の在庫処分 7 |

### **発送地域と物流の影響**

国内販売と海外販売では、ユーザーが感じる「割安感」の構造が異なる。

* **国内市場（Booth）**: 送料込みで25,000円以下に収まることが一つの心理的障壁となっている。メルカリ便などの安価な配送手段を利用し、「総額」での見え方をスマートにすることが重要である 7。  
* **海外市場（Etsy）**: 日本からの送料は30ドルから50ドルに達する。Etsyのアルゴリズムでは「送料込み」の設定が優遇される傾向にあるが、送料を含めた総額に対して決済手数料がかかるため、利益計算を誤ると赤字になるリスクがある 13。海外向けには「Made in Japan」のクラフトマンシップを前面に出し、送料を惜しまない層をターゲットにすべきである。

## ---

**7\. 最終提案：初期販売を成功させるためのロードマップ**

個人クリエイターが「将来的な販売」を見据え、初期段階で実行すべき具体的なアクションを提案する。

### **初期販売に適した価格帯：最有力案**

**「23,800円（税込・送料別）」**

この価格は、2万円台という「こだわり層」が許容する価格帯の中でも安価に見え、かつ1万円以上の利益（工賃）を確保できる、最もバランスの取れた設定である。

### **販売形式と相性の良い戦略**

**「少数ロット・先着即納販売」** 受注生産は初心者が陥りやすい罠である。部材の欠品や制作の遅れが直接的な不信感に繋がるため、まずは「自分が責任を持って完成させた5台」をBoothでゲリラ的に販売し、完売の実績を積み上げるべきである。この「即完売」の事実はSNSでの話題性を呼び、次ロットへの期待値を高める最高の宣伝となる 3。

### **価格以外で勝てる差別化ポイント（3点）**

1. **「日本語ドキュメントと日本国内サポート」の徹底**  
   レバーレスはPCの設定やファームウェアの更新など、初心者には難解な部分が多い。Haute42等の海外製品にはない、丁寧な日本語の導入マニュアルや、Discord等での直接サポートを提供することは、特に初心者層にとって数千円の価格差を凌駕する価値となる。  
2. **「16ボタン」かつ「物理スイッチによるSOCD切替」** 『ストリートファイター6』などの規約変更に即座に対応できるSOCD（上下同時押し時の挙動）の物理スイッチ切り替えや、最新の「16ボタン配置」を標準化する。大手メーカーが慎重になる領域に、技術的な尖りを持って先行することが個人の勝利条件である 3。  
3. **筐体カスタマイズの「体験」を提供** 天板のアクリルを二重にし、ユーザーが自分で印刷したイラストを簡単に、かつ美しく挟める構造にする。さらに、そのイラスト用のテンプレート（PSD/AIデータ）を公式サイトで配布する。ユーザーが「自分のコントローラーを育てる」体験をデザインすることで、製品への愛着を高め、SNSでの写真投稿（UGC）を促進する 3。

以上の調査結果を指針とし、量産品との「価格競争」ではなく、クリエイターとしての「思想と体験の提供」に軸足を置くことで、自作レバーレスコントローラー市場における独自の地位を確立できると確信する。

#### **引用文献**

1. JunkFood Arcade announces price drop on its products : r/fightsticks \- Reddit, 2月 2, 2026にアクセス、 [https://www.reddit.com/r/fightsticks/comments/1bt7pfk/junkfood\_arcade\_announces\_price\_drop\_on\_its/](https://www.reddit.com/r/fightsticks/comments/1bt7pfk/junkfood_arcade_announces_price_drop_on_its/)  
2. スト6におすすめのコントローラーを解説！パッドとアケコンどっちがいい？ \- Hi-Ho, 2月 2, 2026にアクセス、 [https://hi-ho.jp/withgames/column/suto6-controller-recommendation/](https://hi-ho.jp/withgames/column/suto6-controller-recommendation/)  
3. スト6向け！？ボタン増設済薄型レバーレス5選！！｜つき0 \- note, 2月 2, 2026にアクセス、 [https://note.com/tsuki0notes/n/n3f996690f52a](https://note.com/tsuki0notes/n/n3f996690f52a)  
4. 初心者向けレバーレス選定ガイド（2024年3月版）｜ねいあん \- note, 2月 2, 2026にアクセス、 [https://note.com/neianji/n/n773a9e33682a](https://note.com/neianji/n/n773a9e33682a)  
5. Snackbox Micro 2023 : r/fightsticks \- Reddit, 2月 2, 2026にアクセス、 [https://www.reddit.com/r/fightsticks/comments/19dkkcf/snackbox\_micro\_2023/](https://www.reddit.com/r/fightsticks/comments/19dkkcf/snackbox_micro_2023/)  
6. Leverless \- Etsy, 2月 2, 2026にアクセス、 [https://www.etsy.com/market/leverless](https://www.etsy.com/market/leverless)  
7. 【スト6カスタム】レバーレスコントローラー スト6向けボタン配置 アケコン 増設 \- メルカリ, 2月 2, 2026にアクセス、 [https://jp.mercari.com/item/m68549117647](https://jp.mercari.com/item/m68549117647)  
8. Snackbox vs Haute42 : r/fightsticks \- Reddit, 2月 2, 2026にアクセス、 [https://www.reddit.com/r/fightsticks/comments/1cddyab/snackbox\_vs\_haute42/](https://www.reddit.com/r/fightsticks/comments/1cddyab/snackbox_vs_haute42/)  
9. Leverless Controller \- Etsy, 2月 2, 2026にアクセス、 [https://www.etsy.com/market/leverless\_controller](https://www.etsy.com/market/leverless_controller)  
10. Fightstick Leverless \- Etsy, 2月 2, 2026にアクセス、 [https://www.etsy.com/market/fightstick\_leverless](https://www.etsy.com/market/fightstick_leverless)  
11. Snack Box Micro – Junkfood Custom Arcades, 2月 2, 2026にアクセス、 [https://junkfoodarcades.com/collections/snack-box-micro](https://junkfoodarcades.com/collections/snack-box-micro)  
12. Leverless Hitbox \- Etsy, 2月 2, 2026にアクセス、 [https://www.etsy.com/market/leverless\_hitbox](https://www.etsy.com/market/leverless_hitbox)  
13. International shipping and a hard lesson learned. Etsy made a bigger profit than I did on the same sale. Learn from my mistake. \- Reddit, 2月 2, 2026にアクセス、 [https://www.reddit.com/r/Etsy/comments/1gt4zv3/international\_shipping\_and\_a\_hard\_lesson\_learned/](https://www.reddit.com/r/Etsy/comments/1gt4zv3/international_shipping_and_a_hard_lesson_learned/)  
14. 【2026年最新】hitBOXの人気アイテム \- メルカリ, 2月 2, 2026にアクセス、 [https://jp.mercari.com/search?keyword=hitBOX](https://jp.mercari.com/search?keyword=hitBOX)  
15. I don't understand the pricing of shipping costs. : r/Etsy \- Reddit, 2月 2, 2026にアクセス、 [https://www.reddit.com/r/Etsy/comments/18l24qu/i\_dont\_understand\_the\_pricing\_of\_shipping\_costs/](https://www.reddit.com/r/Etsy/comments/18l24qu/i_dont_understand_the_pricing_of_shipping_costs/)
