ShugoYabuno/project-hanoji/docs/deepresearch/market_strategy/レバーレスコントローラー販売戦略分析.md

# **自作レバーレスコントローラー市場における初期発信戦略と競合分析：販売成功へのロードマップ**

## **結論：販売を見据えた初回発信の最適解**

自作レバーレスコントローラーの販売を将来的に見据える個人クリエイターにとって、最初の発信として最も適切な形態は、**「プレイヤーとしての深い課題意識」を起点とし、「設計による解決プロセス」を提示する、物語性の高いnote記事**である。分析の結果、単なる製品のスペック紹介や完成報告のみを行った制作者よりも、既存デバイスへの具体的な不満（入力遅延、ボタン配置の違和感、耐久性不足など）を言語化し、その解決過程を公開している制作者の方が、販売開始時に高い信頼と熱狂的な顧客層を獲得している傾向が顕著である 1。

初回記事において「動機・設計思想・失敗談・次の一手」という構成を採ることは、以下の理由から極めて有効である。

* **信頼の先行獲得**: 失敗談（試作の失敗、基板の不具合など）を隠さず公開することで、制作者の誠実さと、それを克服した最終製品の品質に対する根拠が裏付けられる 4。  
* **共感によるファン化**: 多くの格闘ゲームプレイヤーが抱える「デバイスへの悩み」を言語化することで、読者を「単なる消費者」から「プロジェクトの目撃者・支持者」へと変容させる 1。  
* **販売文脈の自然な導入**: 初回から「売ります」と直球で告知するのではなく、「自分と同じ悩みを持つ人に届けたい」という動機を醸成することで、販売開始時の心理的ハードルを下げ、ブランドのプレミアム性を高めることができる 7。

以下に、競合分析に基づいた詳細な調査結果と戦略的提案を詳述する。

## ---

**1\. 競合クリエイターの発信構造と戦略的分析**

個人・小規模で自作デバイスを販売・発信している先行事例を、収集観点に基づき分析した。

### **1.1 碧井いそめ氏（碧井工房）：課題解決とストーリーテリングの融合**

碧井いそめ氏の発信は、未経験者が理想のデバイスを追求する「物語」として極めて完成度が高い 1。

* **初回発信の目的**: 『ストリートファイター6』（以下、スト6）への本格参戦にあたり、既存のアケコンや安価なレバーレスでは解決できない「入力仕様の差異（スト2とスト6の差）」や「デバイスの物理的な不安定さ」を解消することを宣言している 1。  
* **構成の妙**: 自己紹介から始まり、具体的な「負け筋（デバイスに起因するミス）」を提示し、秋葉原での部品調達というアクションまでを一気に見せる。これにより、読者は制作者の熱量に引き込まれる 1。  
* **信頼性の担保**: 秋葉原の「千石電商」への訪問写真や、使用したパーツ（三和ボタン、Raspberry Pi Pico等）の具体的名称、さらには「1万6千円の格安レバーレスを改造して失敗した話」など、実体験に基づく情報の透明性が非常に高い 1。  
* **販売文脈**: 初回時点では販売に一切触れていない。しかし、後の投稿で「碧井工房」としてのBOOTH展開に繋げており、初期の「純粋な追求」がブランドの信頼ベースとなっている 7。

### **1.2 かぬ氏（かぬコン）：技術的卓越性とニッチ特化**

スマブラ用レバーレス「かぬコン」の制作者であるかぬ氏は、ハードウェアエンジニアリングの側面から信頼を構築している 2。

* **設計思想と信頼性**: 基板設計ツール「KiCad」による回路設計、光造形3Dプリンター「Photon mono 4K」を用いた筐体製作など、アマチュアの域を超えた技術スタックを公開している 2。  
* **独自の価値提案**: スプリングを切断して押下圧を調整し、アクチュエーションポイントを0.2mmまで浅くするという「執拗なまでの調整」を可視化。これが「かぬコン」でなければならない理由として機能している 2。  
* **ビジュアルの使い方**: Fusion 360の設計画面や、積層痕まで見える3Dプリントパーツ、さらには内部配線の美しさなど、工程の可視化によって「中身の伴った製品」であることを証明している 2。

### **1.3 いのまきら氏（いのコン）：コスト透明性とコミュニティ貢献**

オープンソースプロジェクト「Flatbox」をベースにした「いのコン」の事例は、コストパフォーマンスと情報共有に特化している 3。

* **信頼性の担保（実測とデータ）**: 1台あたりの制作費用（18,020円）を円単位で公開し、部品発注先（JLCPCB等）まで明示する。これにより、制作者がマージンを搾取しているのではなく、品質と手間に投資していることが伝わる 3。  
* **失敗の可視化と改善方針**: アクリル板の積層構造（2mm/5mm/2mm/2mm）において、マイコンの厚みを相殺するための設計上の工夫など、具体的な「失敗の回避策」を解説している 3。

### **1.4 競合クリエイター比較表**

| クリエイター | 主な媒体 | 初回のトーン | 販売文脈の濃度 | 信頼性の源泉 | ターゲット層 |
| :---- | :---- | :---- | :---- | :---- | :---- |
| **碧井いそめ** | note/YouTube | 情熱的・挑戦的 | 無（後に販売） | プレイヤー視点の悩み、失敗の公開 | スト6プレイヤー、自作関心層 |
| **かぬ** | note/X | 技術的・専門的 | 控えめな予告 | CAD設計、極限のスイッチ改造 | スマブラ勢、ガチ競技層 |
| **いのまきら** | note | プロセス寄り | 一切触れない | 徹底的なコスト・手順の公開 | 自作勢、低コスト追求層 |

## ---

**2\. 媒体別の特性と発信の役割分担**

初回発信から販売に至るまでの導線設計において、各媒体は異なる役割を担う必要がある。

### **2.1 note：信頼のストックとストーリーの構築**

noteは、制作者の「思考」と「技術」を資産として蓄積するための基盤である 1。

* **長文のストーリー性**: なぜ既存の製品（HitboxやRazer Kitsune、あるいは安価なHaute42等）ではなく、自作に踏み切ったのかという「必然性」を語るのに最適である 1。  
* **技術記録の丁寧さ**: 穴あけのコツや当て板の使用、JLC PCBへの発注手順など、他者が真似できるレベルの情報を出すことで、「この分野の有識者」としての地位を確立できる 2。

### **2.2 X（Twitter）：即時性の高い進捗共有とコミュニティ参加**

Xは、開発の「熱量」をリアルタイムで伝え、潜在顧客と繋がるためのエンジンである。

* **画像の即効性**: 試作機の写真1枚、あるいは基板が届いた瞬間の投稿が、短期間で格ゲー勢の注目を集める 2。  
* **失敗の可視化**: 「3Dプリントに失敗した」「配線を間違えた」といった泥臭い投稿は、完成品に対する期待感を逆に高める効果がある 5。

### **2.3 YouTube：実証と体験の疑似共有**

YouTubeは、文字や写真では伝わりにくい「打鍵音」や「サイズ感」、「プレイ中の安定性」を証明する手段である 8。

* **音声説明の説得力**: 制作者自らがスイッチの選定理由や配置のこだわりを語ることで、専門性が直感的に伝わる。  
* **実測データの提示**: 入力遅延の検証動画や、激しいプレイでもデバイスが動かない様子を見せることで、購入の不安を払拭する 12。

## ---

**3\. 分析アウトプット：成功と失敗の分岐点**

調査に基づき、個人販売における成功パターンと、避けるべきパターンを定義した。

### **3.1 成功パターン（推奨される3つのアプローチ）**

1. **「課題解決の共犯者」パターン（根拠：碧井氏）**: プレイヤーとしての弱点（特定のコンボミスなど）をデバイスのせいにし、それを克服する「最強の武器」を自作する。読者は「自分もその武器があれば勝てるかも」という期待を持ち、販売開始を待ち望むようになる 1。  
2. **「徹底的な透明性」パターン（根拠：いのまきら氏）**: パーツ原価、仕入れ先、設計データを惜しみなく公開する。これにより、「自分で作ると大変だが、この制作者に任せれば適正価格で高品質なものが手に入る」という納得感を生む 3。  
3. **「極限のカスタマイズ」パターン（根拠：かぬ氏）**: 既製品では不可能な「厚さ11mm」「アクチュエーションポイント0.2mm」といった極端なスペックを追求する。汎用品では満足できないハイエンド層を確実にキャッチできる 2。

### **3.2 避けるべきパターン（失敗の3要素）**

1. **「カタログスペックの羅列」**: 「Raspberry Pi Pico搭載」「GP2040-CE採用」といった情報だけでは、安価な大量生産品（Haute42等）と比較され、価格競争に敗北する 12。個人が語るべきはスペックの裏にある「使い心地」である。  
2. **「いきなりの販売告知」**: 制作過程の共有がないまま「作りました、買ってください」と発信すると、信頼性が担保されていないため、特に高額なデバイス（3万円以上）は敬遠される 1。  
3. **「失敗の隠蔽」**: 完璧な完成品のみを見せようとすると、逆に「耐久性は大丈夫か？」「中身は雑なのではないか？」という疑念を招く。自作デバイスにおいて、失敗談は「改善の証」であり、信頼の源泉である 14。

## ---

**4\. 信頼性の担保と技術的裏付け**

販売を視野に入れる場合、以下の要素を初回から段階的に発信することが不可欠である。

### **4.1 ハードウェアの信頼性**

* **筐体の強度**: アクリル板の厚みによる「たわみ」の有無や、20箇所以上のネジ止めによる剛性確保など、具体的な対策を記述する 3。  
* **使用感の実測**: ボタン配置の決定において、コンパスと定規を用いて紙に書き出し、指の動きをシミュレーションしたプロセスを公開する 6。

### **4.2 ソフトウェア（ファームウェア）の専門性**

* **GP2040-CEの活用**: Webコンフィグ画面を用いたカスタム設定（起動ロゴ、SOCDモード、LEDプロファイルなど）を紹介し、最新の競技シーン（SF6のCPTルール等）に対応していることを明示する 16。  
* **低遅延の強調**: デュアルコアCortex-M0+を搭載したRP2040の性能や、USB HIDモードでの応答速度について言及することで、ガチ勢の信頼を獲得する 13。

## ---

**5\. 初回発信における「販売の匂わせ」濃度の推奨**

初回記事における販売への言及は、\*\*「濃度20%」\*\*程度が最適である。

* **推奨される出し方**: 「まずは自分用に究極のものを作る」という目的を100%としつつ、最後に「もし同じ悩みを持つ人がいれば、将来的に数台は形にして提供できる仕組みも考えていきたい」と、可能性を添える程度に留める 2。  
* **理由**: 最初から100%の販売告知をすると、コミュニティは「広告」として認識し、拡散力が低下する。一方で、一切触れないと、後の販売時に「急に金儲けを始めた」という誤解を受けるリスクがある。

## ---

**6\. 最終提案：プロジェクトの初回発信方針**

本プロジェクトに最適な初回発信の方針として、以下の3案を提示する。

### **第1案：【プレイヤー共感型】「負けたくない」を形にする制作記（最有力の推奨案）**

* **コンセプト**: デバイスのせいでコンボを落とした「悔しさ」を原動力にし、それを解決するための「自分だけの正解」を導き出す。  
* **構成**:  
  1. 導入：格ゲーのプレイ歴と、最近感じている「限界」。  
  2. 動機：既存デバイスへの具体的な不満（ボタンが遠い、反応が遅い等） 1。  
  3. 仮説：もし、自分の手のサイズに合わせた、このスイッチを使ったデバイスがあれば？  
  4. アクション：秋葉原への買い出しや基板設計の開始 8。  
  5. 次の一手：試作1号機の完成予定。  
* **理由**: 碧井いそめ氏の成功事例を現代のスト6環境に最適化した、最もファンがつきやすい王道ルートである。

### **第2案：【技術・エルゴノミクス特化型】「身体拡張」としてのデバイス設計**

* **コンセプト**: 「格ゲーは運動である」と定義し、手首や指の負担を極限まで減らすための「エルゴノミクス」を追求する。  
* **ターゲット**: 長時間プレイで手を痛めている層、健康意識の高いゲーマー。  
* **内容**: 指の可動域に基づいたボタン配置の数理的アプローチや、薄型化のための3D設計（Fusion 360）の公開 2。

### **第3案：【コスト・ビルドガイド型】「高品質×低コスト」の民主化**

* **コンセプト**: 5万円する海外製デバイスと同等の性能を、いかに2万円以下の自作で実現するかという「ハック」の側面を強調する。  
* **ターゲット**: 学生や、高価なデバイスに手が出せない層、自作そのものに興味がある層。  
* **内容**: 部品リストの完全公開と、安価に抑えつつも「ここだけは譲れない」という重要パーツ（基板、主要スイッチ）の選定理由 3。

### **初回note記事タイトル案**

1. **「スト6で『あと一歩』勝てない理由を、デバイスの設計から解決することにした」**（第1案向け）  
2. **「なぜ私の指は届かないのか？――手の小さなプレイヤーのための『黄金比』レバーレス制作記」**（第2案向け）  
3. **「総額1万円台でハイエンドを超える。究極の自作レバーレスコントローラー計画始動」**（第3案向け）  
4. **「HitboxでもKitsuneでもない。私が『自分の手』に合わせたコントローラーを自作する必然性」**  
5. **「格ゲー歴10年の結論。昇龍拳が出ない悔しさを、はんだごてに込めることにした」**

## **7\. 初回発信に必要な要素のチェックリスト**

以下の要素を初回note記事に盛り込むことで、販売に向けた盤石な基盤を構築できる。

* \[ \] **強烈な「なぜ（Why）」**: なぜ今、あなたはこれを作るのか？（既存品への不満） 1  
* \[ \] **制作者の顔（人間性）**: 謙虚ながらも、特定の技術やゲームに対する情熱が伝わるか。  
* \[ \] **失敗の予兆/宣言**: 「最初から上手くはいかないだろうが、試行錯誤を公開する」という姿勢 4。  
* \[ \] **具体的な技術キーワード**: GP2040-CE、RP2040、Kailh Choc、基板発注など、専門性を感じさせる用語。  
* \[ \] **美しい「次への引き」**: 試作パーツが届く予定や、具体的な設計の進捗状況。

初回記事として「動機・設計思想・失敗談・次の一手」という構成を採ることは、単なる制作記録を超え、将来の顧客との「信頼の契約」を結ぶ行為である。この構成に、自身のプレイヤーとしてのリアルな言葉を乗せることが、プロジェクト成功の鍵となる。

#### **引用文献**

1. スト6向け最強レバーレスを自作する｜碧井いそめ \- note, 2月 2, 2026にアクセス、 [https://note.com/isomeaoi/n/ne42c021a8c9d](https://note.com/isomeaoi/n/ne42c021a8c9d)  
2. スマブラ用レバーレスコントローラー「かぬコン」をどうやって ..., 2月 2, 2026にアクセス、 [https://note.com/smashbroskanu/n/nc682ae09d907](https://note.com/smashbroskanu/n/nc682ae09d907)  
3. 薄型レバーレスコントローラーは誰でも自作できるという話｜いの, 2月 2, 2026にアクセス、 [https://note.com/inomakira/n/n043fdf0c4d4a](https://note.com/inomakira/n/n043fdf0c4d4a)  
4. 初めてアケコンを作ったので感じたことレポ。 \- note, 2月 2, 2026にアクセス、 [https://note.com/7380\_nanamiya/n/nfd0f76e0e252](https://note.com/7380_nanamiya/n/nfd0f76e0e252)  
5. \[自作レバーレス改造\] 「攻めすぎ」も考えもの...｜ヤマカズ \- note, 2月 2, 2026にアクセス、 [https://note.com/brave\_nerine565/n/nba8ee8fb5f47](https://note.com/brave_nerine565/n/nba8ee8fb5f47)  
6. 箱型自作レバーレスコントローラー作成マニュアル｜khide \- note, 2月 2, 2026にアクセス、 [https://note.com/khide/n/n258c19d409ed](https://note.com/khide/n/n258c19d409ed)  
7. レバーレス作り始めて5ヶ月経過と自己紹介｜碧井いそめ \- note, 2月 2, 2026にアクセス、 [https://note.com/isomeaoi/n/n8f0ee83ad909](https://note.com/isomeaoi/n/n8f0ee83ad909)  
8. スト6向け最強自作レバーレス完成しました！お披露目！あと重大発表！ \- YouTube, 2月 2, 2026にアクセス、 [https://www.youtube.com/watch?v=4TDqjXhTGCk](https://www.youtube.com/watch?v=4TDqjXhTGCk)  
9. 初めての自作アケコン作成記｜ゲム蔵 \- note, 2月 2, 2026にアクセス、 [https://note.com/gamezoo/n/n05270dbf9448](https://note.com/gamezoo/n/n05270dbf9448)  
10. Hitbox Launches "Hitbox Licensing Program" \- explaining they have a patent for the button layout. : r/fightsticks \- Reddit, 2月 2, 2026にアクセス、 [https://www.reddit.com/r/fightsticks/comments/1c1myq8/hitbox\_launches\_hitbox\_licensing\_program/](https://www.reddit.com/r/fightsticks/comments/1c1myq8/hitbox_launches_hitbox_licensing_program/)  
11. Is it even worth it to learn a new control scheme if I'm an average/below average player? : r/Fighters \- Reddit, 2月 2, 2026にアクセス、 [https://www.reddit.com/r/Fighters/comments/15scwu3/is\_it\_even\_worth\_it\_to\_learn\_a\_new\_control\_scheme/](https://www.reddit.com/r/Fighters/comments/15scwu3/is_it_even_worth_it_to_learn_a_new_control_scheme/)  
12. Haute42 C16 Custom Art: The Ultimate Fightstick for Precision, Style, and Competitive Edge, 2月 2, 2026にアクセス、 [https://www.aliexpress.com/p/wiki/article.html?keywords=haute42-c16-custom-art](https://www.aliexpress.com/p/wiki/article.html?keywords=haute42-c16-custom-art)  
13. Haute42 S16-C 16-Button Arcade Stick Controller w/ Kailh Crystal Switches/SOCD | eBay, 2月 2, 2026にアクセス、 [https://www.ebay.com/itm/388657964363](https://www.ebay.com/itm/388657964363)  
14. 新しいキーボードをかったぞ 2023 \- watura, 2月 2, 2026にアクセス、 [https://wtr.io/n/n36fe5c5451d6](https://wtr.io/n/n36fe5c5451d6)  
15. 自分のために始めたキーボード作りがいつの間にか販売デビューしていた件 \- Zenn, 2月 2, 2026にアクセス、 [https://zenn.dev/suikagiken/articles/ec667c024611bf](https://zenn.dev/suikagiken/articles/ec667c024611bf)  
16. 『RPGタイム！〜ライトの伝説〜』構想15年・制作9年 鉛筆で描いて作ったRPGが受賞しまくる理由が遊んでわかった試遊リポート&インタビュー【TGS2021】 | ゲーム・エンタメ最新情報のファミ通.com, 2月 2, 2026にアクセス、 [https://www.famitsu.com/news/202110/01235350.html](https://www.famitsu.com/news/202110/01235350.html)  
17. Releases · OpenStickCommunity/GP2040-CE \- GitHub, 2月 2, 2026にアクセス、 [https://github.com/OpenStickCommunity/GP2040-CE/releases](https://github.com/OpenStickCommunity/GP2040-CE/releases)
