ShugoYabuno/project-hanoji/docs/deepresearch/outreach/initial_outreach_competitive_analysis.md

# 自作レバーレス初期発信の競合分析（Deep Research結果）

## 結論（最初の発信の最適解）
販売を見据えた初回発信は、**プレイヤーとしての課題意識**を起点に、**設計による解決プロセス**を物語として提示するnote記事が最も適切。  
単なるスペック紹介や完成報告だけの発信よりも、**既存デバイスへの具体的不満を言語化し、その解決の試行錯誤を公開する発信**のほうが、販売開始時に強い信頼と熱量のある顧客層を獲得しやすい傾向が確認できる。

この結論は、以下の観点に基づく。
- **信頼の先行獲得**: 失敗談の公開が「誠実さ」と「改善の根拠」になる  
- **共感によるファン化**: 課題を代弁することで読者が「当事者」になる  
- **販売文脈の自然な導入**: 直球の販売告知よりも、動機の共有が後の購入ハードルを下げる

---

## 競合分析：発信構造の要点

### 碧井いそめ氏（碧井工房）
- **主軸**: 課題解決とストーリーテリング  
- **初回の目的**: 既存デバイスの不満（入力の混乱、安価品の不安定さ）の言語化  
- **構成**: 自己紹介 → 不満の具体化 → 行動（部品調達）  
- **信頼性**: 失敗経験の公開、部品名や行動の具体性  
- **販売文脈**: 初期は触れず、後の販売につながる信頼の土台を形成  
- **参考**: https://note.com/isomeaoi/n/ne42c021a8c9d

### かぬ氏（かぬコン）
- **主軸**: 技術的卓越性とニッチ特化  
- **差別化**: 極限のスイッチ改造、詳細な技術スタックの可視化  
- **信頼性**: CAD設計やプリント品質の可視化  

### いのまきら氏（いのコン）
- **主軸**: コスト透明性とコミュニティ貢献  
- **信頼性**: コストの明示、工程の開示、失敗回避の説明  

---

## 媒体別の役割（note / X / YouTube）

### note（信頼の蓄積）
- 長文で「なぜ自作するのか」を語れる  
- 技術記録を丁寧に出すことで「この分野の人」と認識される  

### X（即時性と熱量）
- 進捗の小出しが反応を生む  
- 失敗の写真や短いコメントが共感を集める  

### YouTube（実証と体験共有）
- 打鍵音やサイズ感など、文字では伝わりにくい情報を補完  
- 音声説明の説得力が信頼に直結  

---

## 成功パターン（3つ）
1. **課題解決の共犯者型**  
   プレイヤーの悩みを明確化し、それを解決する制作物語を提示する。
2. **徹底的な透明性型**  
   コスト・工程・失敗を隠さず開示し、納得感を積み上げる。
3. **極限カスタム型**  
   既製品では不可能な仕様に振り切り、明確な理由をつくる。

## 避けるべきパターン（3つ）
1. **カタログスペックの羅列**  
   既製品と比較されやすく、価格競争に巻き込まれる。
2. **いきなり販売告知**  
   信頼が不足しており、読者が離脱しやすい。
3. **失敗の隠蔽**  
   完成品だけの提示は「中身の不安」を招きやすい。

---

## 初回記事の構成評価
「動機・設計思想・失敗談・次の一手」の構成は有効。  
理由は、初回で必要な「信頼・共感・継続性」を同時に満たせるため。

- **動機**: 読者の「自分も同じ悩みがある」への接続点  
- **設計思想**: ただ作るのではなく「なぜそうしたか」が伝わる  
- **失敗談**: 誠実さと改善プロセスが可視化される  
- **次の一手**: 継続の期待が生まれる  

---

## 初回発信における販売の匂わせ濃度
**濃度20%**が最適。  
初回の中心は「自分用に本気で作る」。最後に、同じ悩みを持つ人へ「将来的に少数提供も考える」程度の一文で十分。

---

## 本プロジェクト向け 初回発信方針（3案）

### 案1：プレイヤー共感型（最有力）
- **核**: 体の負担と操作の違和感を、設計で解決する  
- **強み**: エルゴノミクス志向の読者に刺さる  
- **向く構成**: 動機 → 仮説 → 試作 → 失敗 → 次の一手

### 案2：技術・エルゴ特化型
- **核**: 姿勢や可動域の理屈を丁寧に説明  
- **強み**: 専門性と再現性で信頼を得る  

### 案3：コスト・ビルドガイド型
- **核**: 手の届く価格で高品質を目指す  
- **強み**: 自作勢に強い共感を得る  

---

## 推奨案（最有力）
**案1：プレイヤー共感型**  
理由: エルゴノミクスを重視する読者像と完全に一致し、  
「使い続けられる姿勢」という価値を自然に伝えられる。

---

## 初回note記事のタイトル案（3〜5案）
- 分割キーボードの思想を、自作レバーレスに持ち込む理由
- 「姿勢がつらい」を設計で解決する自作レバーレス試作記
- なぜ私は“中立位”を目指すレバーレスを作るのか
- レバーレスの形を、手の角度から考え直す
- 長時間プレイを前提にした自作レバーレスの初期記録

---

## 初回記事の必須要素チェックリスト
- [ ] なぜ今、自作するのか（プレイヤーとしての課題）  
- [ ] 設計思想（中立位・傾き・開きなどの仮説）  
- [ ] 失敗談（試作の課題を具体的に）  
- [ ] 次の一手（長期使用の感想につなげる）  
- [ ] 画像（全体・手の置き位置・失敗の可視化）  

---

## 参考リンク
- https://note.com/isomeaoi/n/ne42c021a8c9d
