ShugoYabuno/project-hanoji/docs/deepresearch/ergonomics/bent_plate_research_2026-01-15.md

# レバーレスコントローラーにおける「天板屈曲（Bent/Sloped Plate）構造」の有効性と、v2試作に向けた設計パラメータの導出

## 序論：格闘ゲーム用入力デバイスにおける人間工学的転換

対戦格闘ゲームの競技シーンにおいて、入力デバイスの進化は目覚ましく、従来のジョイスティックからレバーレスコントローラーへと主役が移り変わっている。この移行の背景には、物理的なレバーの往復運動を廃し、ボタンのみによるデジタル入力を採用することで、入力速度の極限化と正確性の向上を図るという力学的合理性がある。

しかし、現在市場に流通している多くのレバーレスコントローラーは、製造コストや加工の容易さを優先した結果、平坦なアクリル板や金属板を用いたフラットパネル構造に留まっている。自作レバーレスコントローラー「Project Hanoji」の次世代プロトタイプ（v2）開発において検討されている「天板屈曲（Bent/Sloped Plate）構造」は、この平坦な設計が孕む人間工学的な課題を根本から解決するための野心的な試みである。

人間の手は解剖学的に平面ではなく、緩やかな弧を描き、各指は異なる長さと運動軌道を持っている。天板に意図的な角度や曲面を導入することは、単なる視覚的なデザインの変更ではなく、腱の張力、関節の可動域、そして神経の圧迫といった生理学的な諸条件を最適化し、長時間の競技におけるパフォーマンス維持と健康被害（RSI：反復性緊張損傷）の防止を両立させるための必然的な進化と言える。

本報告書では、ガフロ製作所の「LI.TERAS mini」に代表される先行プロダクトの分析を起点とし、エルゴノミクスキーボードの世界で培われた「キーウェル（Key Well）」や「親指クラスター」の知見を統合する。さらに、指の屈曲動作に関する運動学的研究を参照しながら、Project Hanoji v2に直接適用可能な具体的な設計パラメータ（寸法、角度、形状）を導出することを目的とする。

## 先行プロダクトの構造分析とユーザー体験の評価

天板屈曲構造の有効性を検証するためには、すでに実用化されている、あるいはコミュニティベースで洗練されてきた既存のデバイスを解剖学的な視点から精査する必要がある。

### ガフロ製作所「LI.TERAS mini」におけるスロープ実装の意図

ガフロ製作所が提供する「LI.TERAS mini」は、従来のレバーレスコントローラーの概念を拡張し、ユーザーが左右のデバイスを自由に組み合わせることができるモジュール構造を採用している。その中でも「右側スロープ（Right Slope）」ユニットは、本調査において極めて重要なベンチマークである。

このスロープ構造の最大の目的は、ボタンを「指の腹」で押下することを容易にし、打鍵に必要な指のストローク距離を短縮することにある。一般的なフラットパネルでは、指を垂直に立てて叩く「ピアノ打ち」が推奨されるが、これは特定の腱に負荷を集中させやすく、特に小指や薬指において操作の難易度を高める傾向がある。

LI.TERAS miniのスロープ角は、ユーザーが標準的な姿勢で手を置いた際、右肩がわずかに上がった状態になる程度に設定されており、これによって指が自然にボタン面に覆いかぶさるような配置を実現している。しかし、ユーザーレビューからは重要な副作用も報告されている。傾斜をつけることでボタン位置が相対的に高くなるため、適切なパームレストによる手首の支持がない場合、右手首を常に折り曲げた（背屈または掌屈）状態で固定しなければならず、これが手首への負担増大を招くという指摘である。

この知見は、天板の「屈曲」を検討する際、パームレスト（支持面）と打鍵面（作用面）の相対的な高度差を如何に制御すべきかという、Project Hanoji v2における決定的な設計課題を浮き彫りにしている。

### エルゴノミクスキーボードにおける「お椀型」と「親指クラスター」

自作キーボード界隈、特に「Dactyl Manuform」や「Glove80」といったプロダクトは、天板屈曲の究極形とも言える「キーウェル（Concave Key Well）」構造を長年追求してきた。これらのデバイスは、指が曲がる際の軌道に合わせてキーを立体的に配置することで、指の移動距離を最小化している。

特に「Dactyl Manuform」の進化過程は示唆に富む。初期のDactylでは親指クラスターが比較的高い位置に配置されていたが、Manuformでは親指を下方向（垂直方向の負のオフセット）に移動させ、手の自然な握り込みに近い位置で動作するように設計変更された。これは、レバーレスコントローラーにおいて最も酷使される「親指ボタン（ジャンプボタン等）」の配置に対し、平面的な延長線上ではなく、一段低い、あるいは角度のついた独立した面としての配置が有利であることを示している。

| デバイス名 | 構造形式 | 主な屈曲・傾斜の狙い | 評価・課題 |
| :--- | :--- | :--- | :--- |
| **LI.TERAS mini (Slope)** | 平面屈曲 | 指の腹での打鍵を容易にし、入力速度を向上させる。 | 指の入りやすさは向上するが、手首への負担には注意が必要。 |
| **Dactyl Manuform** | 立体曲面 | 各指のリーチを均一化し、親指の可動域を最適化する。 | 高い快適性を持つが、スイッチの固定や配線が複雑。 |
| **Glove80** | 超低背曲面 | CMC関節を固定したまま全キーへのリーチを可能にする。 | 手の平を動かさずに操作可能。打鍵後の戻りもスムーズ。 |
| **Kinesis Advantage2** | 固定曲面 | 手首の pronation（回内）と extension（伸展）を最小化する。 | 腱への負担が大幅に軽減されるが、慣れが必要。 |

### 先行事例から導き出される「距離」と「角度」の相関

先行事例を詳細に観察すると、パームレストの終端（折れ目、またはエッジ）からボタンの中心までの距離には、人間の手のサイズに基づいた一定の法則性が認められる。

一般成人の手の長さ（中指先端から手首の最初のしわまで）が約17.5cm、手の平の幅が約8cmであることを考慮すると、指の第2関節（PIP関節）が屈曲ラインに位置する場合、**ボタン中心までの距離は35mmから50mmの範囲に収束する**。

LI.TERAS mini等のスロープ付きモデルでは、この距離に加えて、約15度から25度の傾斜角（スロープ角）が設定されていると推測される。角度を急にするほど「指の腹」で押しやすくなる反面、手首が浮いてしまうため、パームレスト側の高さを調整し、手首が水平（ニュートラル）を保てるように設計することが、先行事例が示唆する成功の要諦である。

## 人間工学とバイオメカニクス：指の軌道と力学的必然性

天板を曲げる、あるいは角度をつけるという設計の根拠は、人間の手の解剖学的な運動特性に深く根ざしている。平坦な板の上にボタンを並べる行為は、物理的には簡潔であるが、生理学的には「指の屈曲（Flexion）」という本来の動きを阻害している側面がある。

### 指の屈曲軌道の解析：円弧か、垂直か

解剖学的な知見によれば、指の先端が屈曲運動を行う際に描く軌道は、手のひら（または前腕の延長線上の平面）に対して垂直な直線ではなく、特定の中心点を持つ「円弧（Arc）」あるいは「楕円（Ellipse）」に近い。

具体的には、深指屈筋（FDP）の働きにより、指先は「巻き込み（Roll-up）」ながら手のひらに近づいていく。この際、指の各関節（DIP, PIP, MCP）は同時に屈曲を開始するのではなく、荷重条件や筋肉の負荷に応じて順次連動する。

ボタン面が平坦な場合、指がボタンを押し込む際のベクトルと、ボタンのスイッチが沈み込む軸（Stem）の方向が、ストロークの途中で乖離してしまう。天板を屈曲させ、ボタン面を指の腹の側に傾けることは、この「押し込みベクトル」と「スイッチの軸方向」を一致させ、エネルギーの伝達効率を最大化することを意味する。

### 「曲げ」による力学的・医学的メリット

天板屈曲構造を導入することで得られる具体的なメリットは、以下の3点に集約される。

1.  **腱への静的負荷の軽減**:
    平面配置では、指をボタンの上に「待機」させる際、手首を背屈（伸展）させる必要がある。これは手首の伸筋群に持続的な緊張を強いるが、天板を奥に傾ける（Negative Tilt）ことで、手首をニュートラルな角度（約10度から15度の軽度伸展）に保つことができ、手根管内の圧力を最小限に抑えられる。

2.  **打鍵スピードへの影響（長さ-張力関係）**:
    筋肉は、その静止時の長さの約1.2倍のときに最大の張力を発揮できる（Length-Tension Relationship）。天板が屈曲し、指が軽く丸まった「自然な構え（Claw Grip）」の状態でボタンを捉えられるようになると、筋肉は最も効率的な収縮範囲で動作でき、瞬発的な入力速度が向上する。

3.  **リーチの均一化**:
    小指や親指は、中指に比べて短く、可動域も異なる。平面では小指が「届かない」あるいは「無理に伸ばす」必要があるが、小指エリアの天板を内側に曲げる、あるいは全体を凹型にすることで、全指がリラックスした状態でホームポジションを維持できる。

### 過度な屈曲に伴うリスク要因と生理学的弊害

一方で、角度をつけすぎること（オーバースロープ）は、別の重大なリスクを招く。

*   **過度な掌屈（Downward Bend）**:
    ネガティブ・チルトを15度から20度以上に設定しすぎると、手首が不自然に下側に折れ曲がり、正中神経を圧迫する。これは「手首の過度な屈曲」による神経障害（手根管症候群に似た症状）を引き起こす要因となる。

*   **「ピペット・サム（Pipette Thumb）」**:
    親指クラスターの角度が親指の自然な対向運動（Opposition）の軌道と一致しない場合、親指の付け根（CMC関節）に過度な剪断力がかかり、腱鞘炎（De Quervain's tenosynovitis）を誘発する恐れがある。

*   **指の滑りとスイッチの側圧**:
    傾斜が強すぎると、指先がボタンの表面で滑りやすくなる。また、スイッチの軸に対して斜めから力がかかるため、軸の摩擦（Scratchiness）が増大し、スイッチの寿命や反応速度に悪影響を与える可能性がある。

## Project Hanoji v2に向けた設計パラメータの導出

以上の先行事例分析と解剖学的知見に基づき、Project Hanoji v2試作機にそのまま適用可能な具体的な設計パラメータを算出した。本パラメータは、製造の容易さと人間工学的効果のバランスを考慮し、単純な平面の組み合わせ（多面体構造）を前提としている。

### 推奨寸法と配置パラメータ

以下の数値は、平均的な成人男性の手のサイズ（手長175mm-180mm）を基準としている。

| パラメータ項目 | 推奨値（目安） | 設計上の意図・根拠 |
| :--- | :--- | :--- |
| **Ridge（折れ目）の位置** | パームレスト終端から **40mm - 45mm** | 第2関節（PIP）の位置に折れ目を設定し、指先の「巻き込み」をカバーする。 |
| **スロープ傾斜角（前方）** | **10° - 15°** (Negative Tilt) | 手首の背屈を抑制し、前腕と手の甲を一直線に近づける。 |
| **左右の開き角（Hanoji角）** | 各 **10° - 20°** (Tenting) | 前腕の pronation（回内）を抑え、尺骨と橈骨が平行に近い状態を作る。 |
| **親指ボタンの高度差** | 4指平面より **-5mm - -8mm** (下降) | 親指の自然な下降運動（握り込み）に合わせ、親指クラスターを低く配置する。 |
| **Ridgeからボタン中心まで** | $x = 30 \text{mm} \times \cos(\theta)$ | 角度 $\theta$ に応じてボタン中心を配置。指が最も力強く押せるリーチを維持。 |

### 形状の選択：Polyhedral（多面体） vs Curved（曲面）

製造難易度と効果のトレードオフを検討した結果、v2試作機においては**「Polyhedral（多面体）」**構造を強く推奨する。

*   **製造の容易さ**: 連続的な曲面（Curved）をアクリルや金属で作成するには、加熱成型や高度な5軸切削が必要だが、多面体であればV字の溝を入れた後の「曲げ加工」や、3Dプリントにおける面出しが極めて容易である。
*   **スイッチ固定の安定性**: スイッチ（ボタン）は平面に対して垂直に固定されるように設計されている。連続曲面にボタン穴を開けると、スイッチのフランジ部分と天板の間に隙間が生じ、ガタつきの原因となる。多面体構造（各ボタン群がそれぞれの平面に配置される設計）であれば、この問題を回避できる。
*   **モジュール性の維持**: Dactyl Manuformのパラメータ調整が示す通り、多面体であれば各平面の角度をスクリプト（OpenSCAD等）で容易に変更でき、ユーザーごとのカスタマイズが現実的となる。

### 力学的・数学的モデルによる補足

ボタンの押し込み力 $F_{input}$ を、スイッチの軸方向への有効力 $F_{effective}$ と、軸への側圧 $F_{lateral}$ に分解すると以下のようになる（角度 $\alpha$ は指の押し込みベクトルとスイッチ軸のなす角）。

$$F_{effective} = F_{input} \cdot \cos(\alpha)$$
$$F_{lateral} = F_{input} \cdot \sin(\alpha)$$

天板の屈曲角を調整することで $\alpha$ を $0$ に近づけることが、摩擦抵抗を減らし、最速のレスポンスを実現するための物理的な正解である。

## 設計時に回避すべき「落とし穴（Failure Modes）」

試作段階で陥りやすい失敗パターンを以下に列挙する。これらを事前に排除することで、手戻りを最小限に抑えることが可能である。

1.  **エッジの鋭利さ（The Sharp Ridge Problem）**:
    天板を屈曲させる際、その折れ目（Ridge）が鋭利な角のままであると、パームレストから指を移動させる際に手のひらの付け根や指の腹を痛める原因となる。折れ目には必ず $R2.0\text{mm}$ 以上の丸みをつけるか、緩衝材を配置すべきである。

2.  **不連続なパームレスト（Disconnected Palm Support）**:
    天板に角度をつけたが、パームレストが水平な机の上に置かれたままである状態。これにより、手のひらの一部が宙に浮き、結果として特定の筋肉（総指伸筋など）が常に緊張を強いられる。パームレストは必ず天板の傾斜に合わせて一体成型、あるいは角度調整されるべきである。

3.  **親指と人差し指の衝突（Thumb-Index Collision）**:
    Dactyl Manuformの失敗例として挙げられるのが、親指クラスターを内側に寄せすぎることによる干渉である。ボタンを密集させすぎると、親指でジャンプボタンを押す際、親指の付け根が人差し指のボタン（弱パンチ等）に接触し、誤入力を引き起こす。

4.  **材料の剛性不足（Structural Weakness）**:
    屈曲させた天板は、平面よりも応力が集中しやすい。特にアクリル板を使用する場合、折れ目の部分は強度が低下するため、内部に補強の支柱（Standoff）を配置する、あるいは板厚を $3\text{mm}$ 以上に設定するなどの対策が必要である。

## 結論とProject Hanoji v2への提言

本調査を通じて、レバーレスコントローラーにおける「天板屈曲構造」は、単なるエルゴノミクスの模倣ではなく、格闘ゲームという極限の反応速度が求められる環境において、身体的ポテンシャルを最大限に引き出すための必然的な進化であることが明らかとなった。

Project Hanoji v2においては、先行プロダクトの「LI.TERAS mini」が示したスロープの有用性と、「Dactyl Manuform」が証明した親指の下方オフセットの重要性を統合すべきである。具体的には、**「左右独立した15度のテンティング」と「奥側への10度のネガティブ・チルト」を組み合わせた多面体天板**を試作のベースラインとすることを推奨する。

また、設計パラメータの導出において最も重要なのは、特定の固定値に固執することではなく、ユーザーの打鍵スタイル（指の腹で押すか、指先で押すか）に合わせて **Ridge からボタン中心までの距離（35mm-50mm）** を微調整できる柔軟性を持たせることである。

v2プロトタイプが、平面という物理的な制約から解放され、人間の手の自然な動きに寄り添う形状を実現することで、レバーレスコントローラーの新たなスタンダードを提示することを期待する。本報告書で詳述した解剖学的根拠と設計パラメータは、長時間のプレイにおける健康維持のみならず、デバイスとの一体感を高めることで、プレイヤーの意思を1フレームの遅延もなくゲーム内へと伝えるための強固な理論的支柱となるはずである。
