ShugoYabuno/project-hanoji/docs/deepresearch/ergonomics/ergonomics_research_summary.md

# 分割・エルゴノミクスキーボードに関する調査要約とProject Hanojiへの適用

## 1. 調査概要
本ドキュメントは、分割式およびテンティング機能付きキーボードのエルゴノミクス設計に関する知見を整理したものです。特にテンティング角度のユーザー選好データと、医学的・解剖学的な設計原則についてまとめています。

---

## 2. エグゼクティブサマリー

分割式・テンティング付きキーボードのエルゴノミクス設計知見を整理しました。
テンティング角度は約**10～15°を基本**とし、ユーザーの前腕回内（手のひら下向き）を軽減し自然な「握手」姿勢に近づけます。

- **推奨角度**: 多くのユーザーは10°や20°の適度な傾斜を好み、30°以上の極端な傾斜は少数派です。
- **配置の原則**: 左右のキー部を肩幅程度に離し「ハの字」に開くことで手首の尺側偏位（小指側への曲がり）を抑制し、肘・肩をより自然な位置に保ちます。
- **パームレスト**: 手首が真っ直ぐになる高さに設計し、角の当たりを和らげる処理が重要です。
- **安定性**: 膝上で安定させるにはハーフを一体化するプレートや滑り止めが有効です。

総じて、適度なテンティングと分割配置は筋骨格への負担軽減に有効ですが、過度な角度は姿勢調整や安定性とのトレードオフになるため、ユーザーの使用環境に合わせた**可変設計**が望まれます。

---

## 3. エルゴ設計の原則まとめ（用語と定義）

### 前腕の回内 (Pronation)・回外 (Supination)
- **定義**: 前腕を内側（回内）/外側（回外）に回す動き。
- **課題**: 一般的なキーボードでは手のひらが下向き＝強い回内状態になり、尺骨と橈骨が交差して筋を圧迫し血流も阻害します。
- **解決**: 適度に回外（親指側を上げる）したニュートラルな前腕角度に保つことで、筋緊張や圧迫を軽減できます。テンティングの目的はこの姿勢を実現することです。

### 尺側偏位 (Ulnar Deviation)・橈側偏位 (Radial Deviation)
- **定義**: 手首を小指側（尺側）/親指側（橈側）に曲げる動き。
- **課題**: 標準の直線配置キーボードでは、両手首が外側（小指側）に折れる「尺側偏位」が常態化し、手根管内の神経圧迫の原因となります。
- **解決**: 分割キーボードで左右の距離や角度（ハの字）を調整し、手首が前腕から真っ直ぐ伸びるように配置します。

### 手首の伸展 (Wrist Extension)
- **定義**: 手首を手の甲側に反らせる動き。
- **課題**: キーボードが高い、または奥が高い（正傾斜）と手首が反り（伸展）、血流低下や痛みの主要因となります。
- **解決**: キーボードを低く保つか、パームレストで高さを埋め、**ニュートラルティルト**（手首が横から見て真っ直ぐ）な状態を維持します。テンティング時は手首が浮きがちになるため特に重要です。

### 肘の開きと肩の外転
- **課題**: 一体型キーボードでは両手が中央に集まり、肩が内側にすぼまる（巻き肩）姿勢になりがちです。
- **解決**: 分割キーボードを肩幅に広げることで、肘を体側に保ち、胸を開いたリラックスした姿勢が可能になります。

---

## 4. 「テンティング角」実データと推奨レンジ

Dygma社の調査（Raiseユーザー計1000名以上）による、各角度に対するユーザー評価の割合データです。

| 角度 | Uncomfortable (不快) | Ok (妥当) | Favourite (お気に入り) |
| :--- | :--- | :--- | :--- |
| **10°** | 9.2% | 51% | **40.6%** |
| **20°** | 3.8% | 62.3% | **36%** |
| **30°** | 25.5% | 58.2% | 18% |
| **40°** | 56.5% | 37.7% | 7.9% |

### 分析
- **10°～20°がスイートスポット**: もっとも好まれる角度帯であり、不快と感じるユーザーも極めて少ない「安全圏」です。
- **30°以上はニッチ**: 角度がきつくなるほど「お気に入り」の割合は減り、「不快」が急増します。40°では過半数が不快と感じています。

### 角度レンジごとの特性

#### 0～5°（フラットに近い）
- **メリット**: 従来の操作感に近く違和感が少ない。机や椅子の調整が不要。
- **デメリット**: 回内状態が続き、エルゴノミクス効果（疲労軽減）は限定的。
- **ユーザーの声**: 「フラットでは結局快適でなく、数日で角度をつけた」

#### 5～10°（低めのテンティング）
- **メリット**: 初心者が移行しやすい。手首のひねりが若干改善し、長時間使用での疲労が軽減される。
- **デメリット**: 劇的な改善ではないため、既に症状がある人には不十分な場合がある。

---

## 5. Project Hanoji への適用と見解

本調査結果に基づき、Project Hanojiの製品設計およびマーケティングにおいて以下の点を推奨します。

### ① 設計目標角度の最適化
- **メイン・ターゲット**: **10°～20°**
  - 多くのユーザー（約75%以上）が「お気に入り」または「妥当」と感じるこのレンジを、製品のデフォルトまたは最も安定して使える角度として設定すべきです。
  - 現在の競合（Victrixの6°）よりも明確に高いエルゴ効果を訴求でき、かつ30°のような「慣れが必要な角度」よりも導入障壁が低くなります。

### ② 可変機構（Adjustability）の重要性
- データが示す通り、ユーザーによって快適な角度は異なります（ある人にとってのベストな30°が、別の人には不快）。
- **提案**:
  - 固定式ではなく、**交換可能な脚（Legs/Wedges）**や、無段階調整可能な機構を取り入れる。
  - エントリーモデルではコストを抑えるため「15°固定」とし、ハイエンドモデルで「可変」を提供するのも戦略として有効です。

### ③ 「膝上プレイ」への配慮
- 分割・テンティングの弱点は「安定性」です。特に格闘ゲームのような激しい入力を行う場合、傾斜したデバイスは横滑りしやすくなります。
- **提案**:
  - 左右のユニットを連結し、膝上で安定させるための**「ドッキング・プレート」**（調査にある"Platform"）をオプションまたは標準で用意する。
  - 底面の滑り止め素材には特にこだわる必要があります。

### ④ パームレストの一体設計
- テンティングを行うと、手首の位置が高くなり「手首の伸展（反り）」が起きやすくなります。これを防ぐため、**傾斜に追従するパームレスト**は必須です。
- 筐体と一体化させるか、専用のリストレストを付属させることで、ユーザーに正しい「ニュートラルティルト」を提供できます。

### ⑤ マーケティング・メッセージ
- 専門用語（回内、尺側偏位）は補足的に使用し、**「自然な握手姿勢（Natural Handshake Position）」**という直感的な言葉でテンティングのメリットを伝えます。
- 「10°の魔法」のように、わずかな傾斜が大きな疲労軽減を生むことをアピールポイントとします。

### ⑥ 試作v1検証からのフィードバック (2026-01-15追加)
- **パームレストの重要性再確認**: 傾斜のみでパームレストがない場合、重力で手が滑りやすく、常に保持するための力が必要となることが実機テストで確認されました。
- **「ハの字」配置の必須化**: テンティング角（Z軸回転）のみでは、手首を甲側（背屈/伸展）に曲げる不自然な力がかかることが判明しました。XY平面での角度付け（ハの字）を組み合わせることが、手首の負荷軽減には不可欠です。
