ShugoYabuno/project-hanoji/content/assets/prototypes/2/IMG_20260118_211157364.jpg

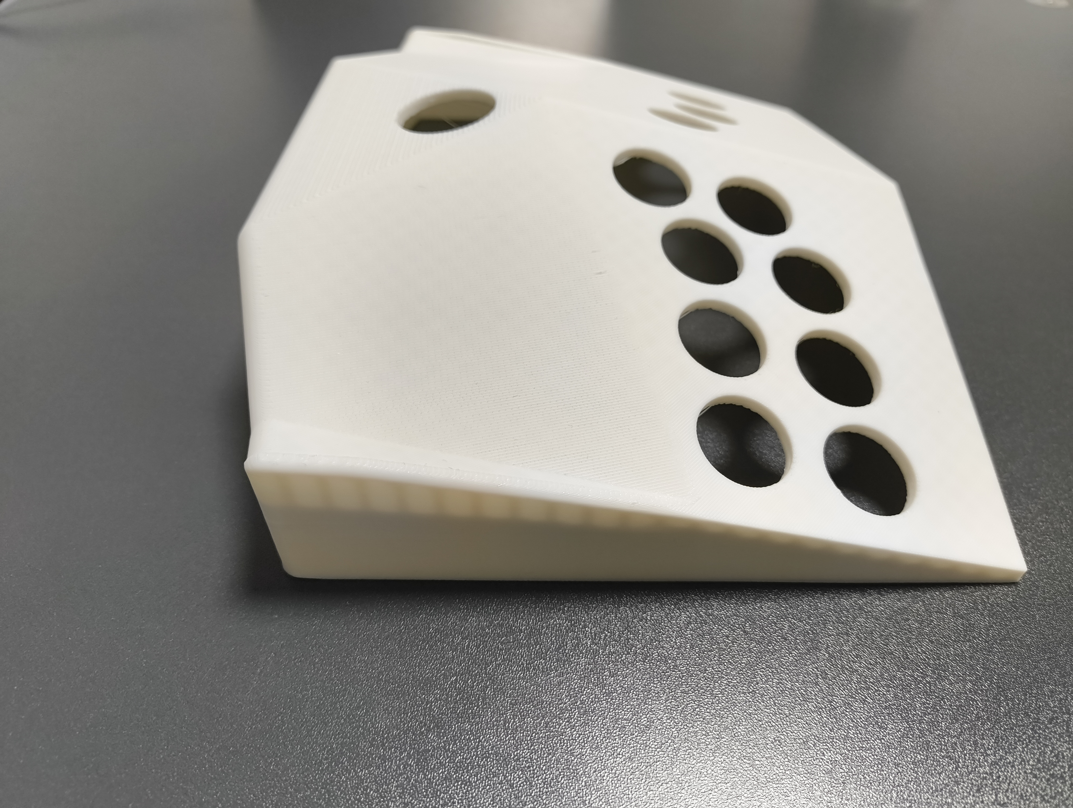
content/assets/prototypes/2/IMG_20260118_211157364.jpg
